propann/dexed/doc/Audio-Chain.png

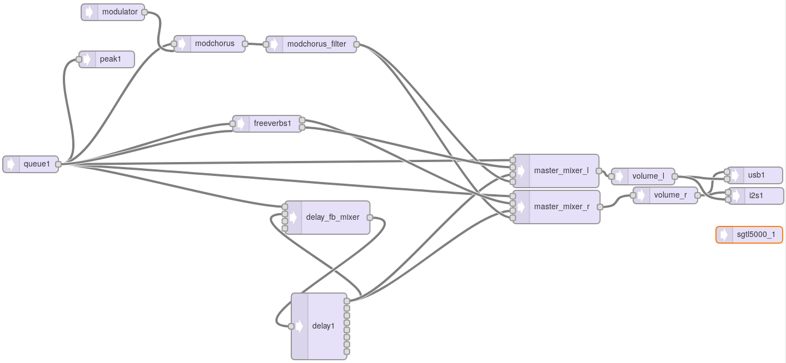
doc/Audio-Chain.png
