propann/dexed/doc/Build_InstructionsV3_Capacitive_Touch/MD_Capacitive_Touch_pcb_overview.png

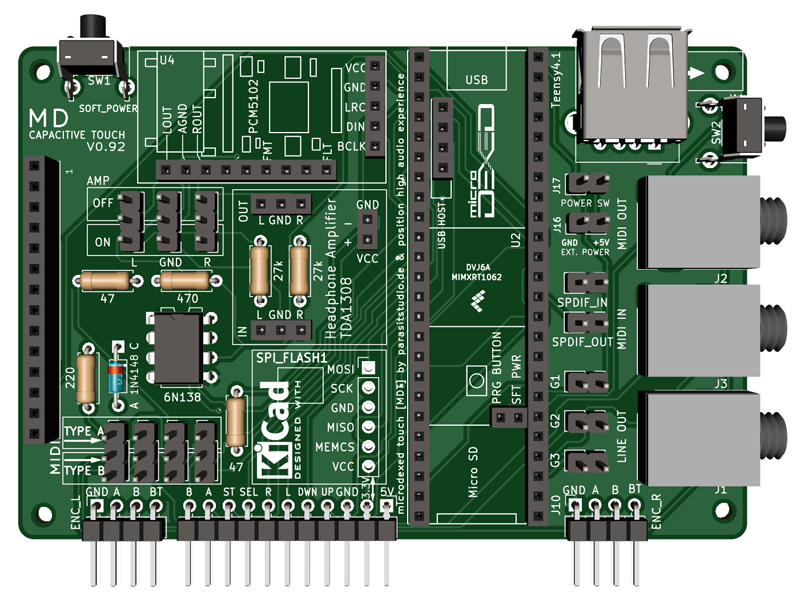
doc/Build_InstructionsV3_Capacitive_Touch/MD_Capacitive_Touch_pcb_overview.png
