propann/dexed/doc/Display-Conversion/back.jpg

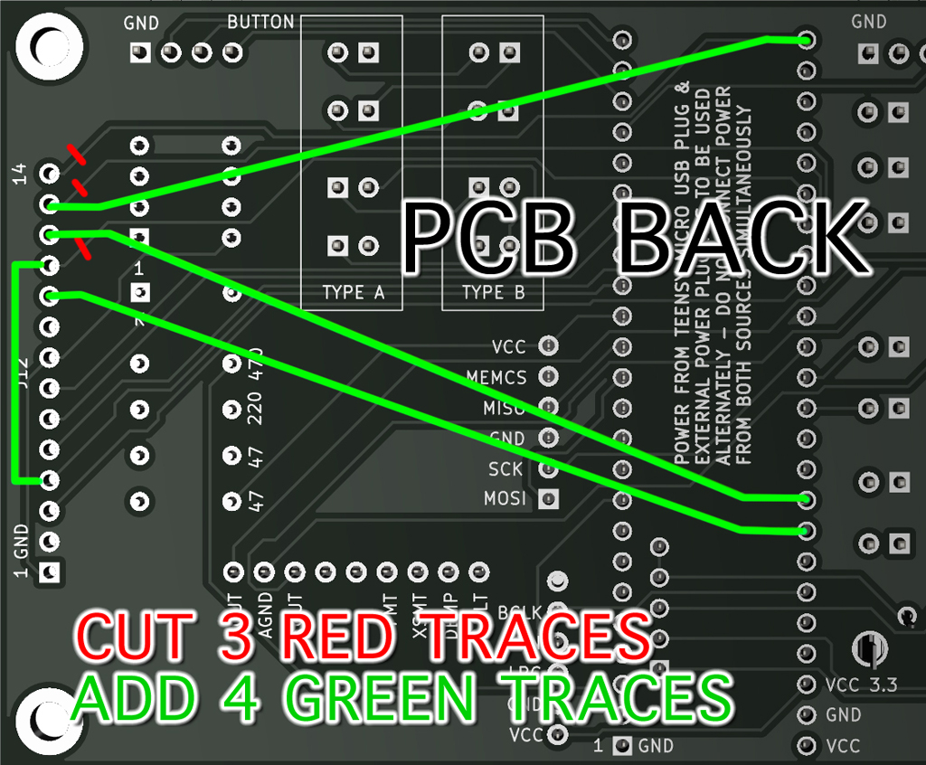
doc/Display-Conversion/back.jpg
