propann/dexed/doc/Display-Conversion/front.jpg

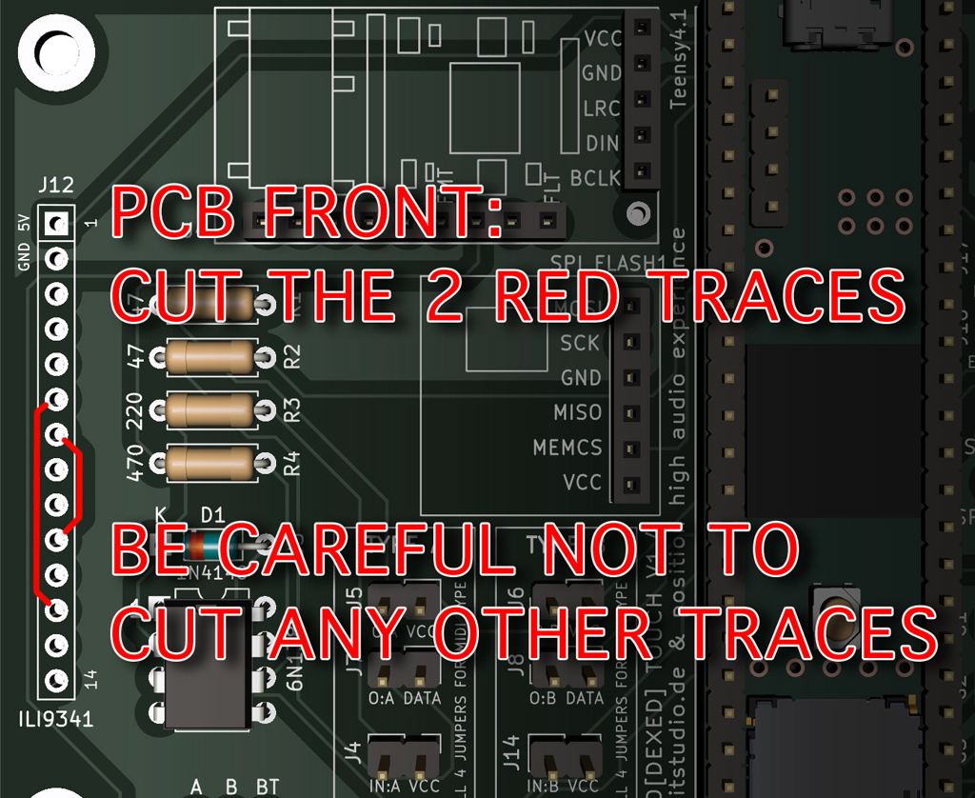
doc/Display-Conversion/front.jpg
