propann/dexed/doc/display-wire.png

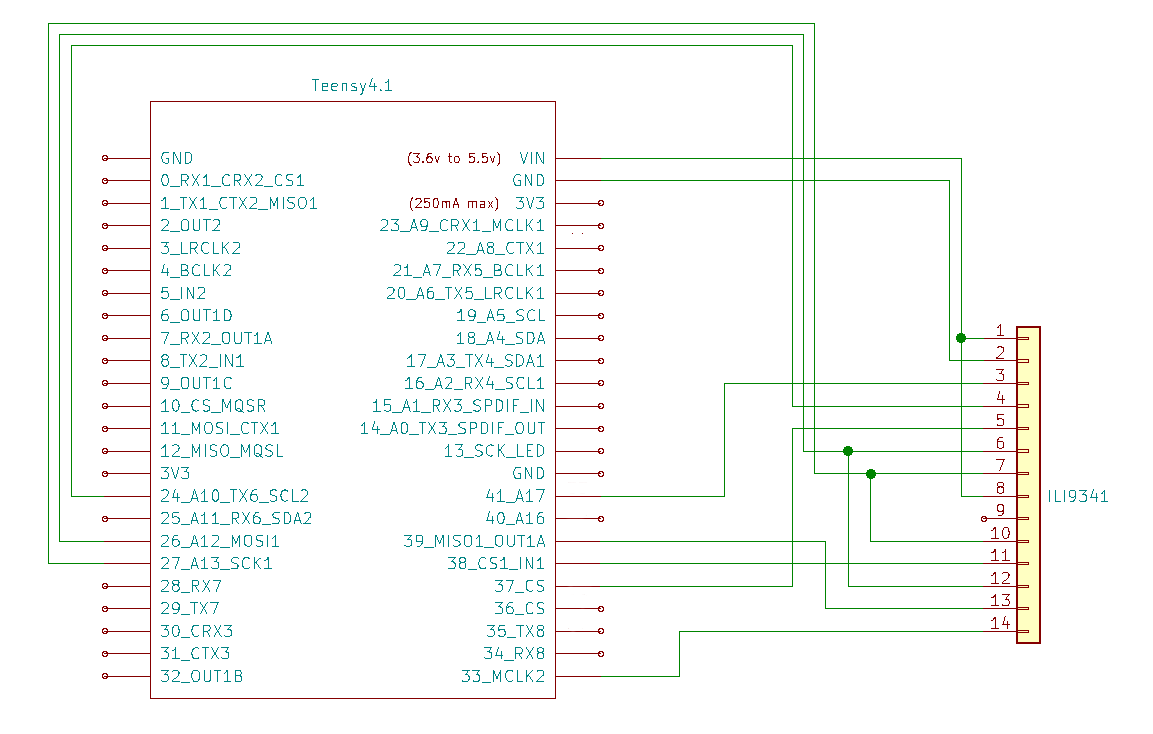
doc/display-wire.png
