propann/dexed/doc/Gamepad/gamepad.png

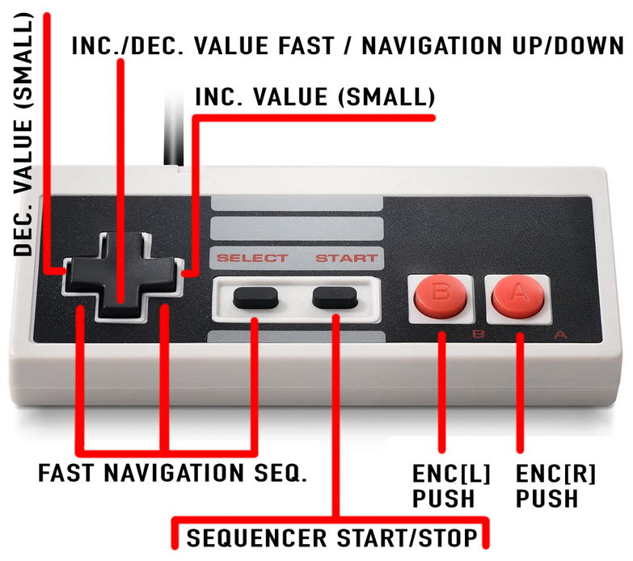
doc/Gamepad/gamepad.png
