propann/dexed/doc/gen1-gen2.jpg

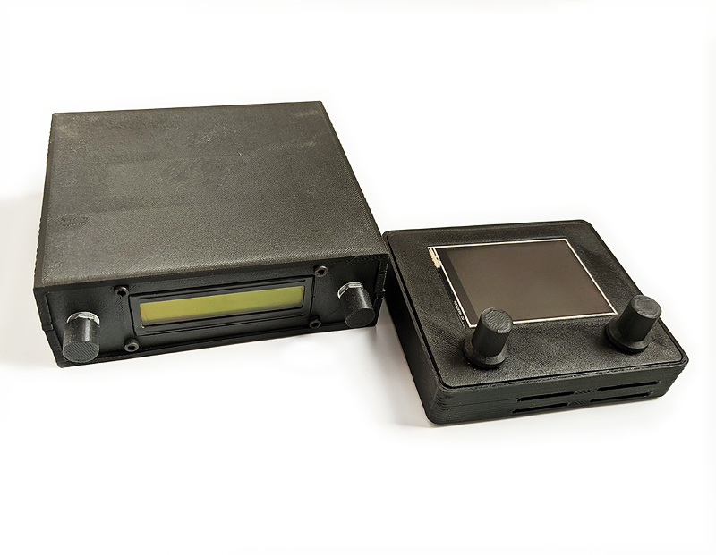
doc/gen1-gen2.jpg
