propann/dexed/doc/MicroDexed-Audio-FlowChart.png

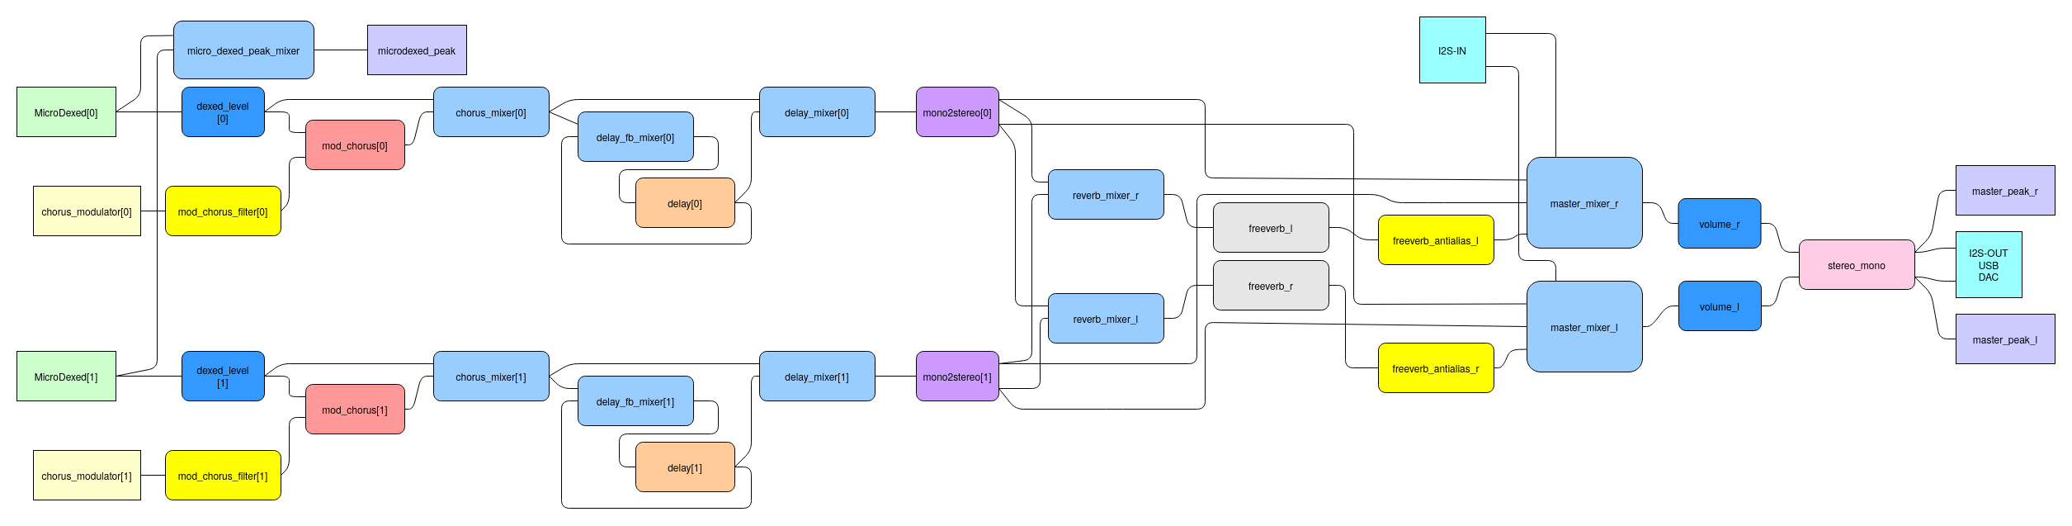
doc/MicroDexed-Audio-FlowChart.png
