propann/dexed/doc/pin_layout_t41.png

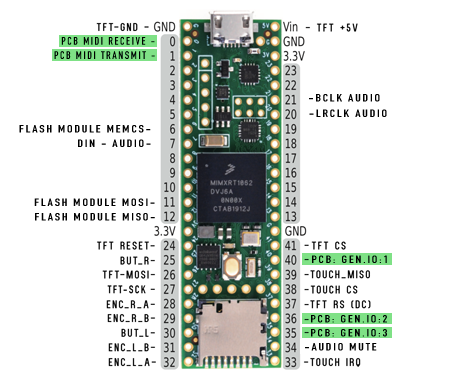
doc/pin_layout_t41.png
