propann/dexed/doc/proto-a-b1.jpg

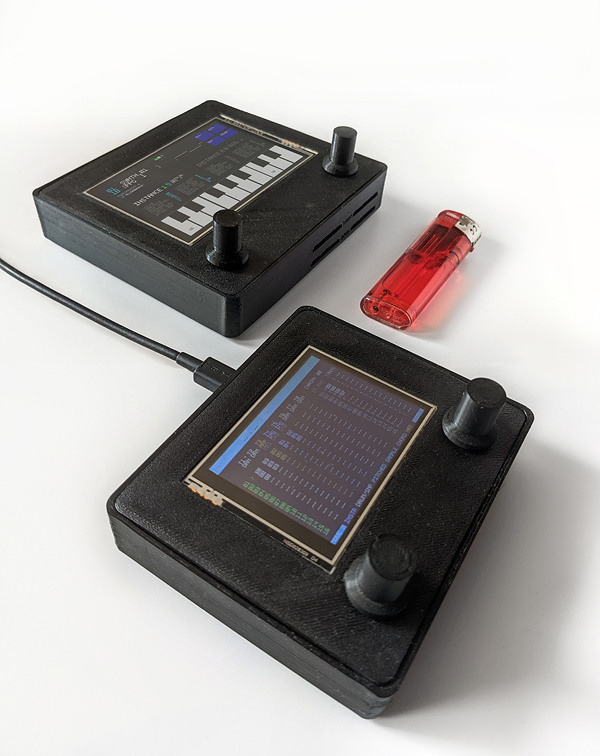
doc/proto-a-b1.jpg
