propann/dexed/doc/proto-b1.jpg

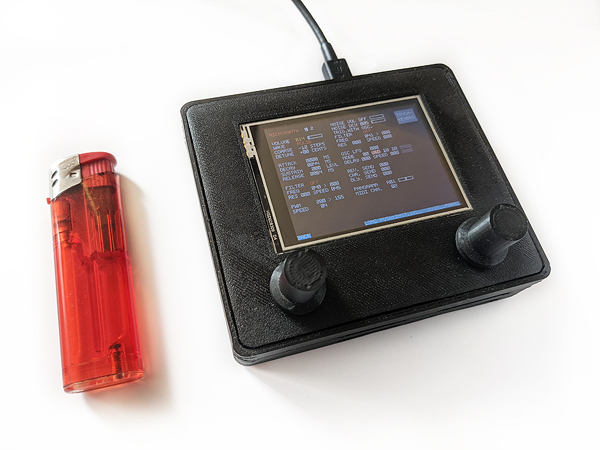
doc/proto-b1.jpg
