propann/dexed/doc/Build_InstructionsV2/assembly_final3.jpg

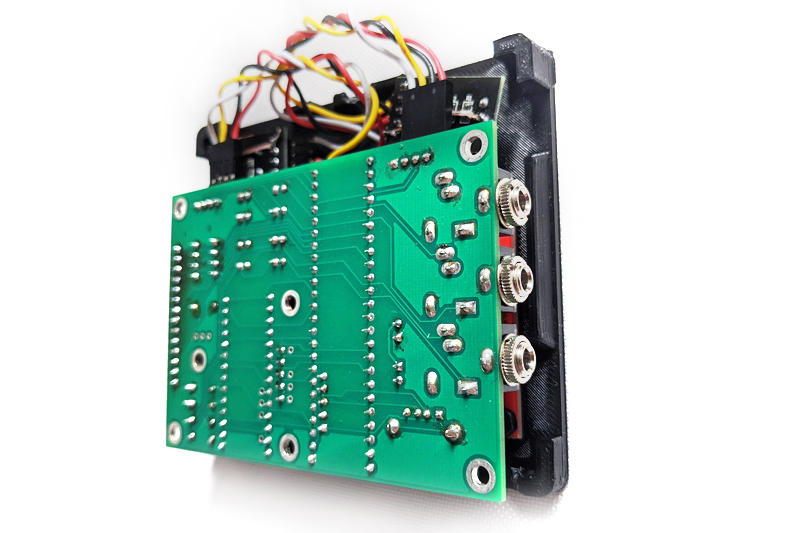
doc/Build_InstructionsV2/assembly_final3.jpg
