propann/dexed/doc/Build_InstructionsV2/assembly_final6.jpg

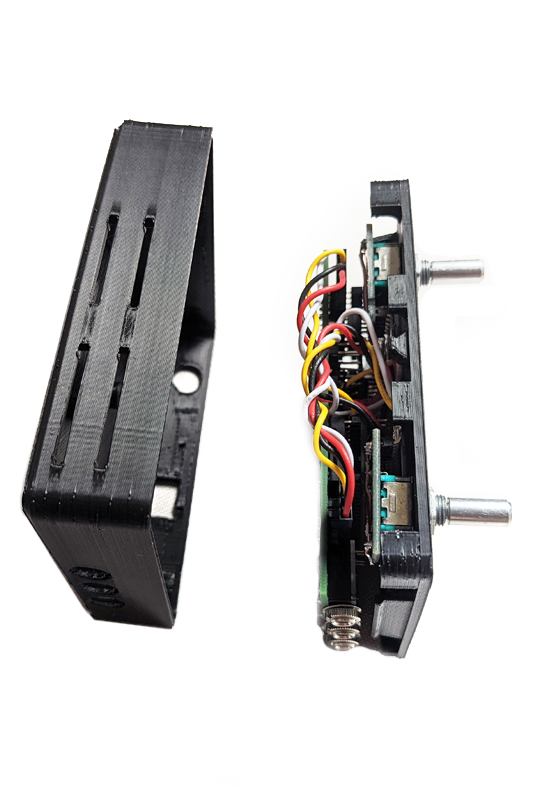
doc/Build_InstructionsV2/assembly_final6.jpg
