propann/dexed/doc/Build_InstructionsV2/back-c.png

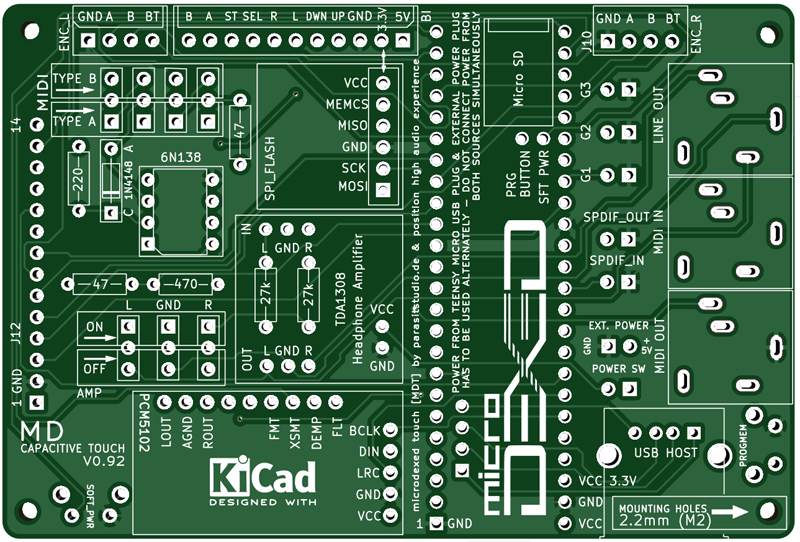
doc/Build_InstructionsV2/back-c.png
