propann/dexed/doc/Build_InstructionsV2/board-assembled3.png

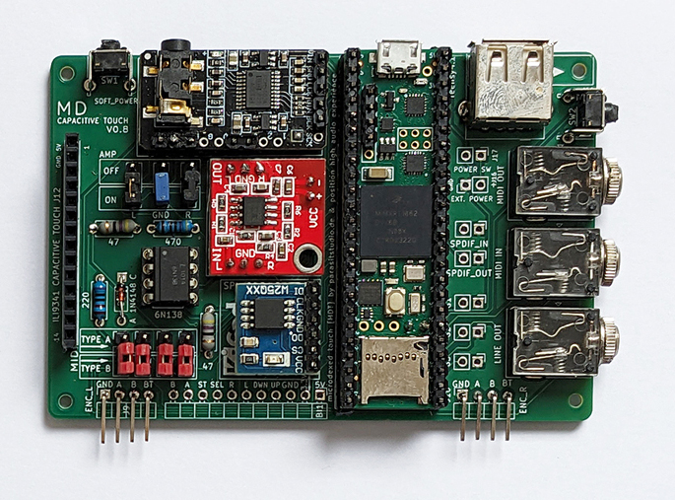
doc/Build_InstructionsV2/board-assembled3.png
