propann/dexed/doc/Build_InstructionsV2/board-with-flash2.png

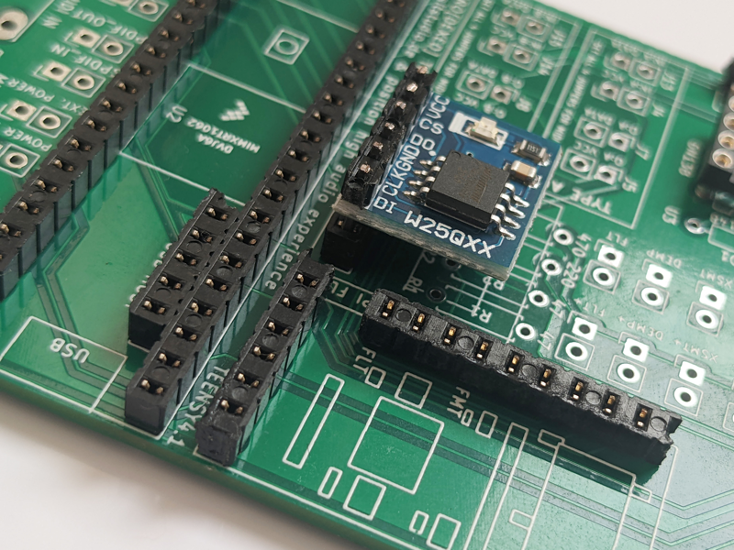
doc/Build_InstructionsV2/board-with-flash2.png
