propann/dexed/doc/Build_InstructionsV2/board-with-flash-c.png

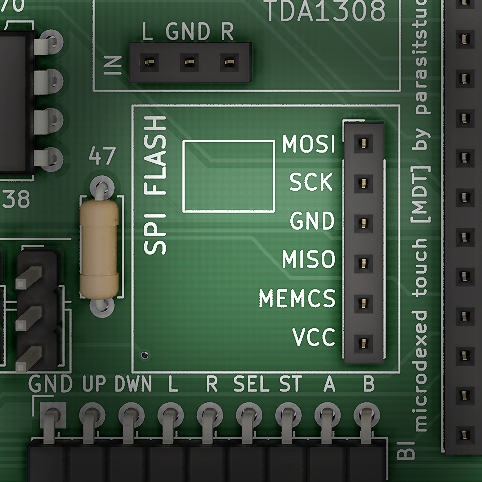
doc/Build_InstructionsV2/board-with-flash-c.png
