propann/dexed/doc/Build_InstructionsV2/board-with-flash.png

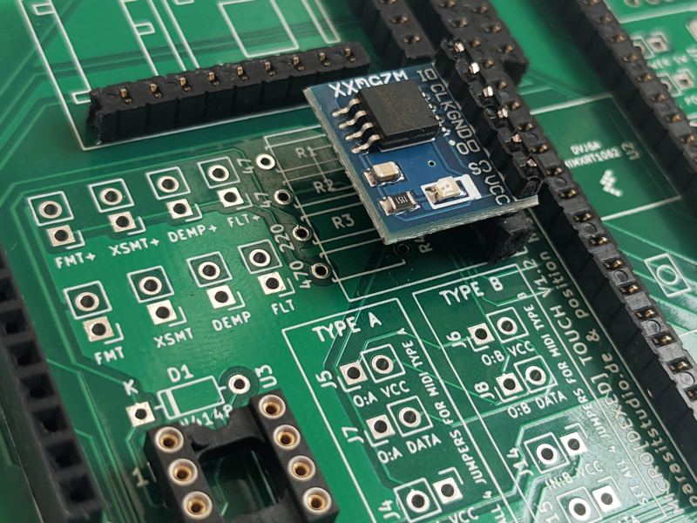
doc/Build_InstructionsV2/board-with-flash.png
