propann/dexed/doc/Build_InstructionsV2/board-with-sockets1.png

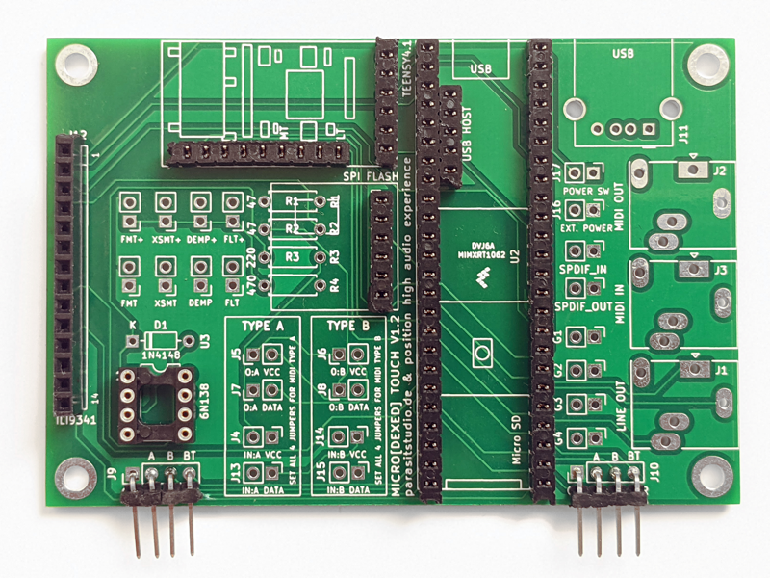
doc/Build_InstructionsV2/board-with-sockets1.png
