propann/dexed/doc/Build_InstructionsV2/board-with-sockets2.png

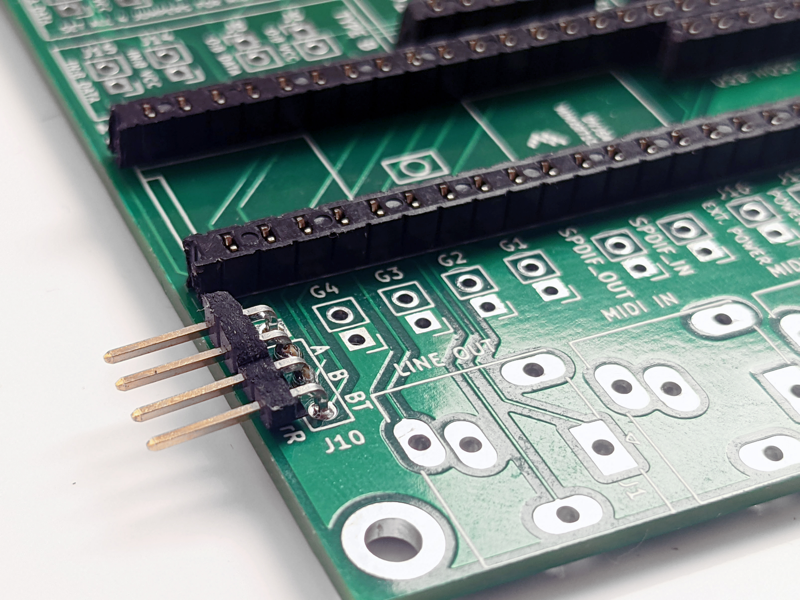
doc/Build_InstructionsV2/board-with-sockets2.png
