propann/dexed/doc/Build_InstructionsV2/bottomcase.png

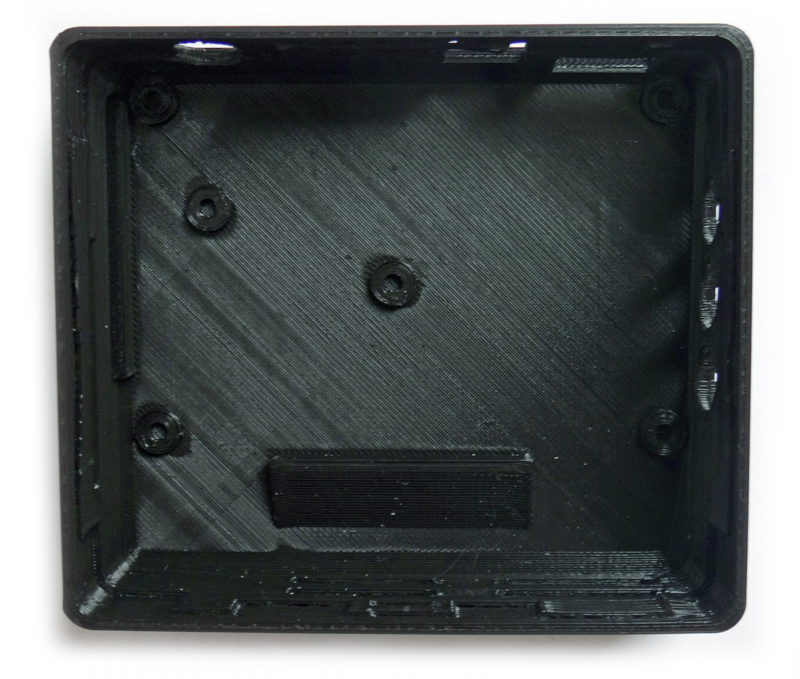
doc/Build_InstructionsV2/bottomcase.png
