propann/dexed/doc/Build_InstructionsV2/case-sdmod-lid-cover.png

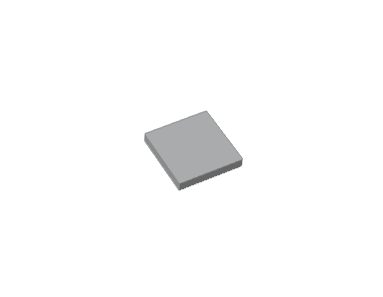
doc/Build_InstructionsV2/case-sdmod-lid-cover.png
