propann/dexed/doc/Build_InstructionsV2/case-sdmod-lid.png

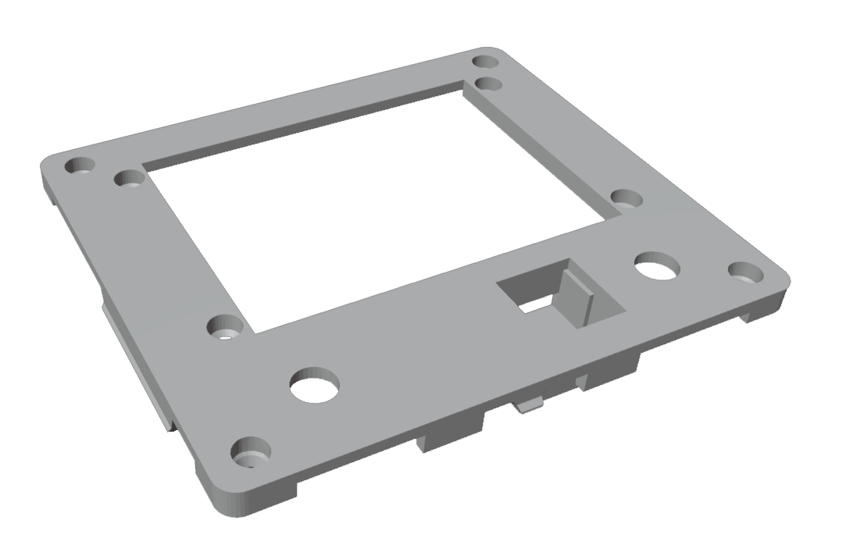
doc/Build_InstructionsV2/case-sdmod-lid.png
