propann/dexed/doc/Build_InstructionsV2/case.png

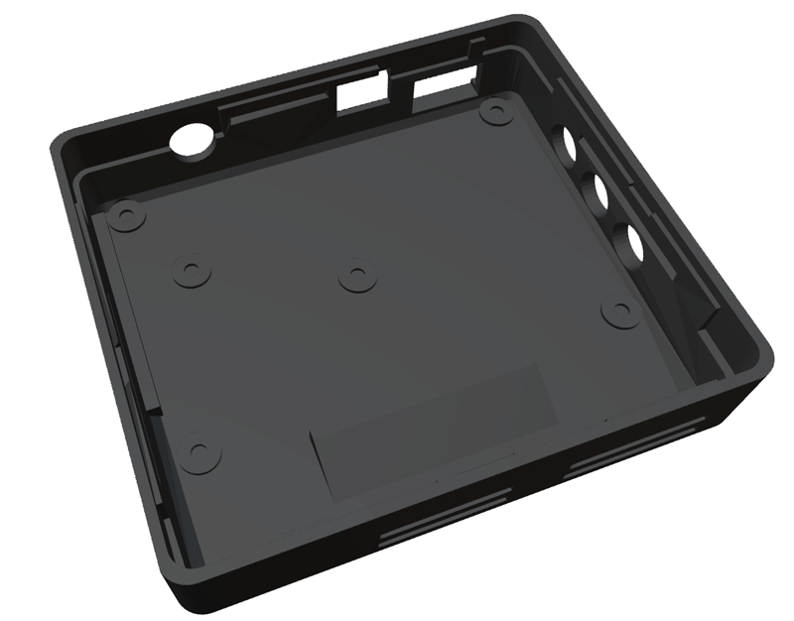
doc/Build_InstructionsV2/case.png
