propann/dexed/doc/Build_InstructionsV2/case_0.jpg

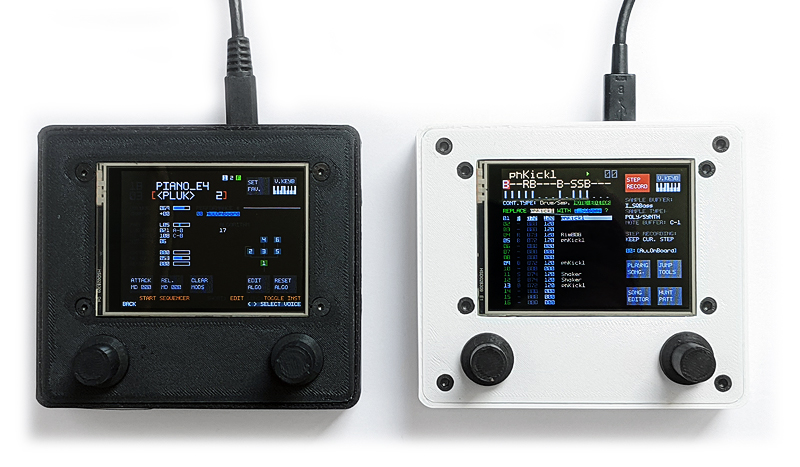
doc/Build_InstructionsV2/case_0.jpg
