propann/dexed/doc/Build_InstructionsV2/case_1.jpg

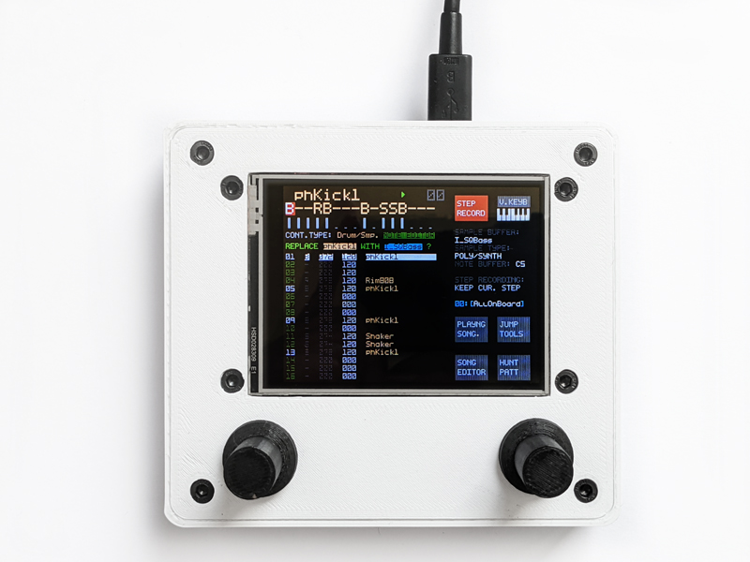
doc/Build_InstructionsV2/case_1.jpg
