propann/dexed/doc/Build_InstructionsV2/case_2.jpg

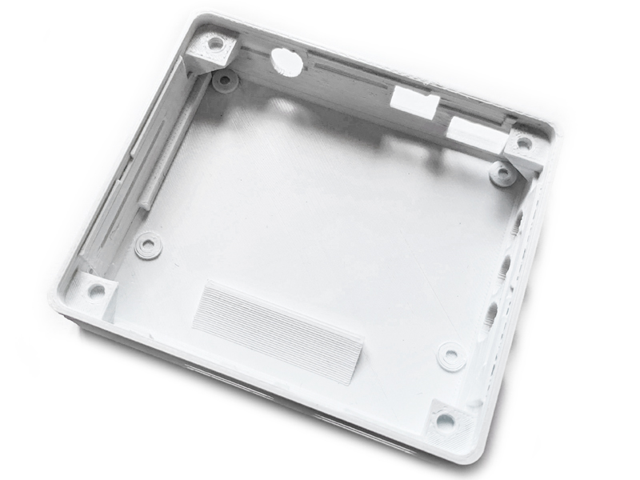
doc/Build_InstructionsV2/case_2.jpg
