propann/dexed/doc/Build_InstructionsV2/case_3.jpg

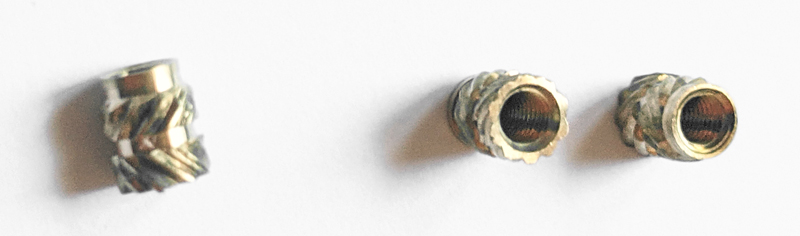
doc/Build_InstructionsV2/case_3.jpg
