propann/dexed/doc/Build_InstructionsV2/case_3b.jpg

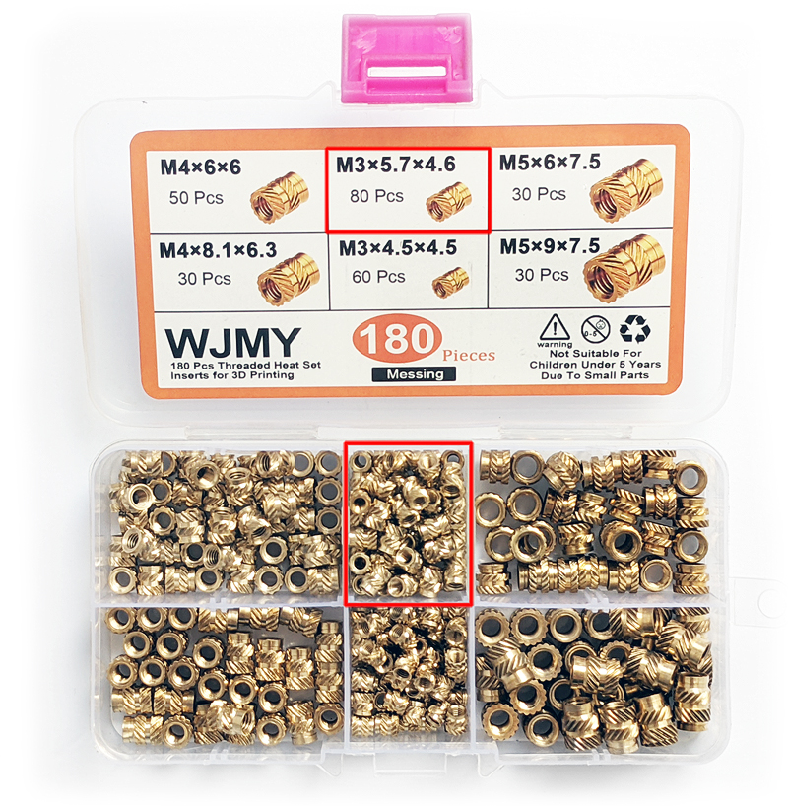
doc/Build_InstructionsV2/case_3b.jpg
