propann/dexed/doc/Build_InstructionsV2/case_4.jpg

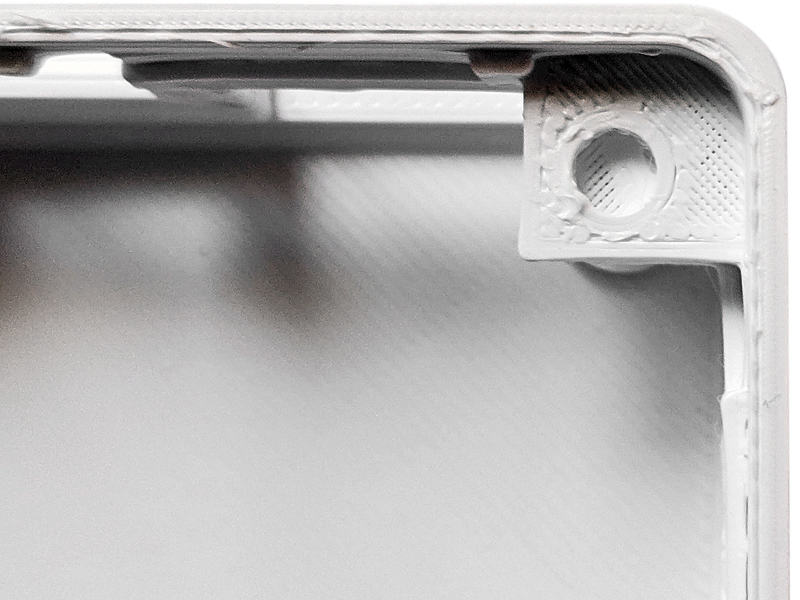
doc/Build_InstructionsV2/case_4.jpg
