propann/dexed/doc/Build_InstructionsV2/case_5.jpg

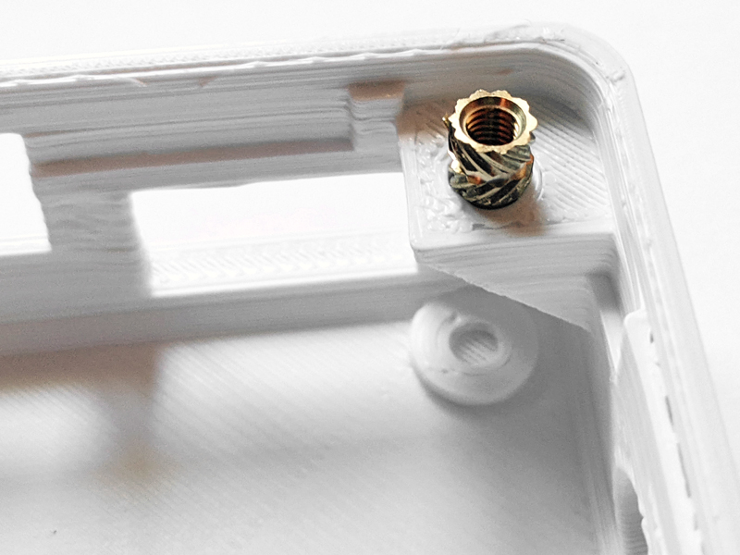
doc/Build_InstructionsV2/case_5.jpg
