propann/dexed/doc/Build_InstructionsV2/case_6.jpg

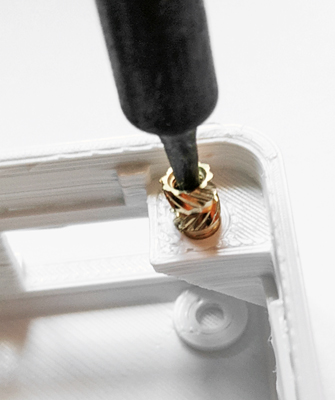
doc/Build_InstructionsV2/case_6.jpg
