propann/dexed/doc/Build_InstructionsV2/case_7.jpg

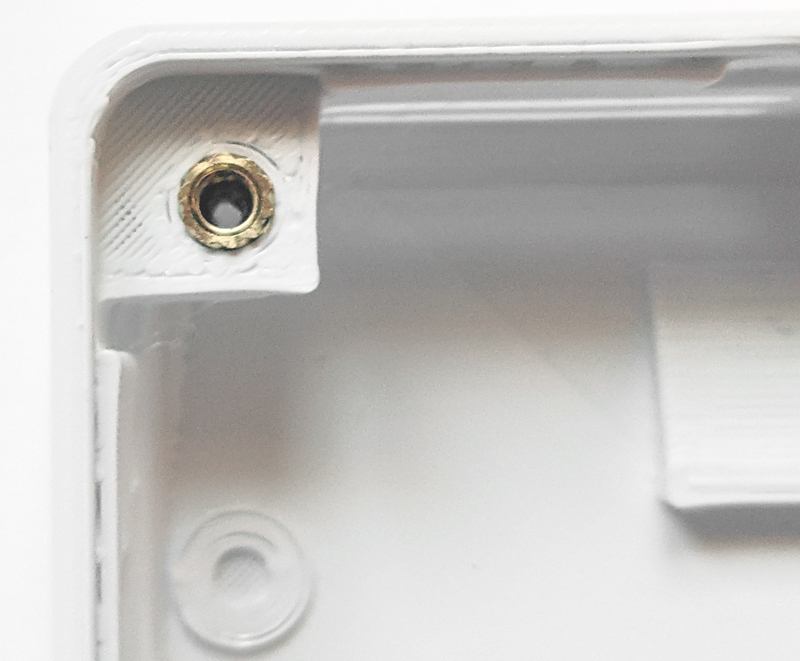
doc/Build_InstructionsV2/case_7.jpg
