propann/dexed/doc/Build_InstructionsV2/case_8.jpg

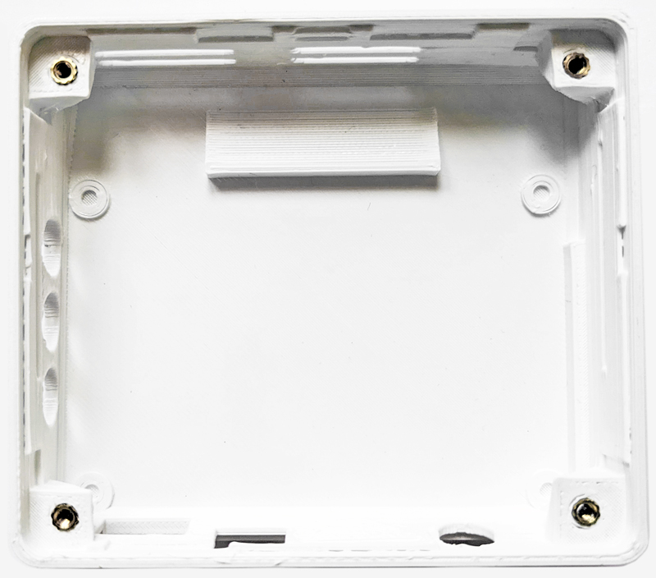
doc/Build_InstructionsV2/case_8.jpg
