propann/dexed/doc/Build_InstructionsV2/case_9.jpg

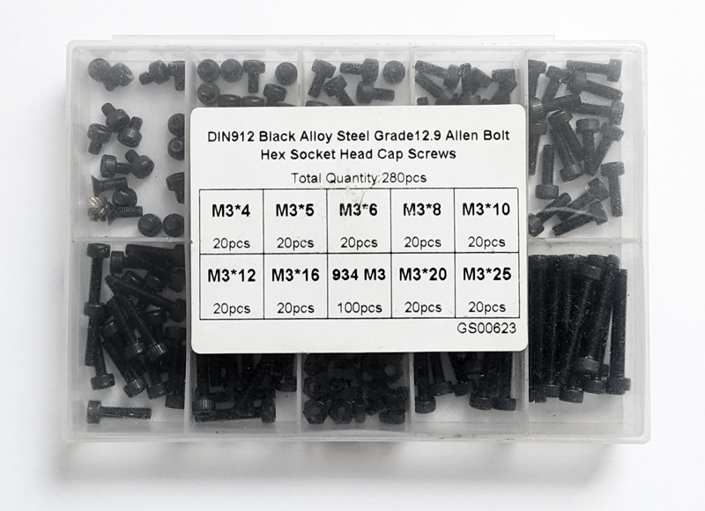
doc/Build_InstructionsV2/case_9.jpg
