propann/dexed/doc/Build_InstructionsV2/case_10.jpg

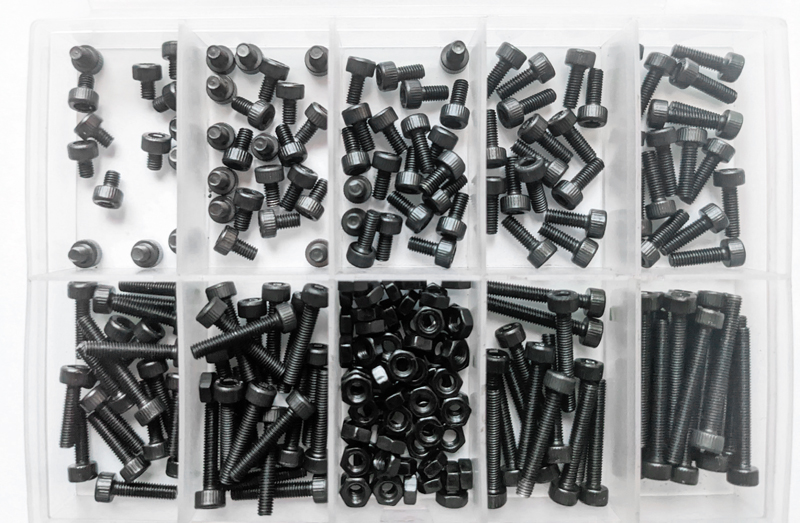
doc/Build_InstructionsV2/case_10.jpg
