propann/dexed/doc/Build_InstructionsV2/case_11.jpg

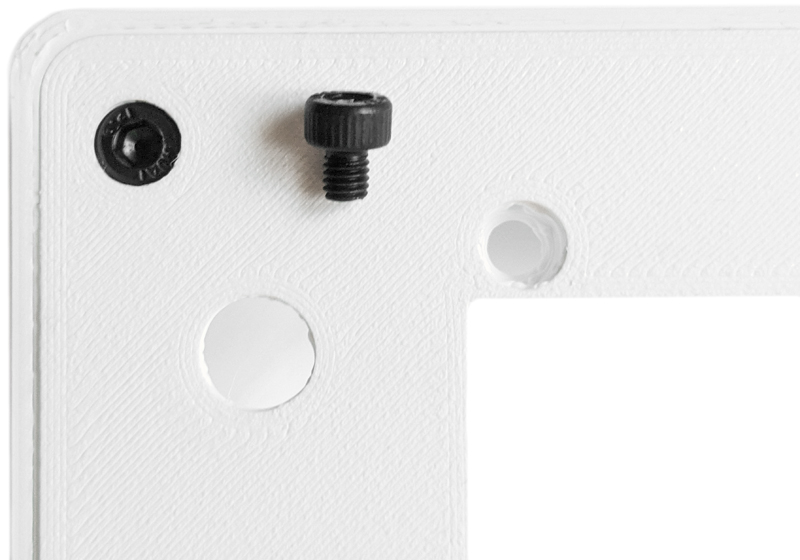
doc/Build_InstructionsV2/case_11.jpg
