propann/dexed/doc/Build_InstructionsV2/case_12.jpg

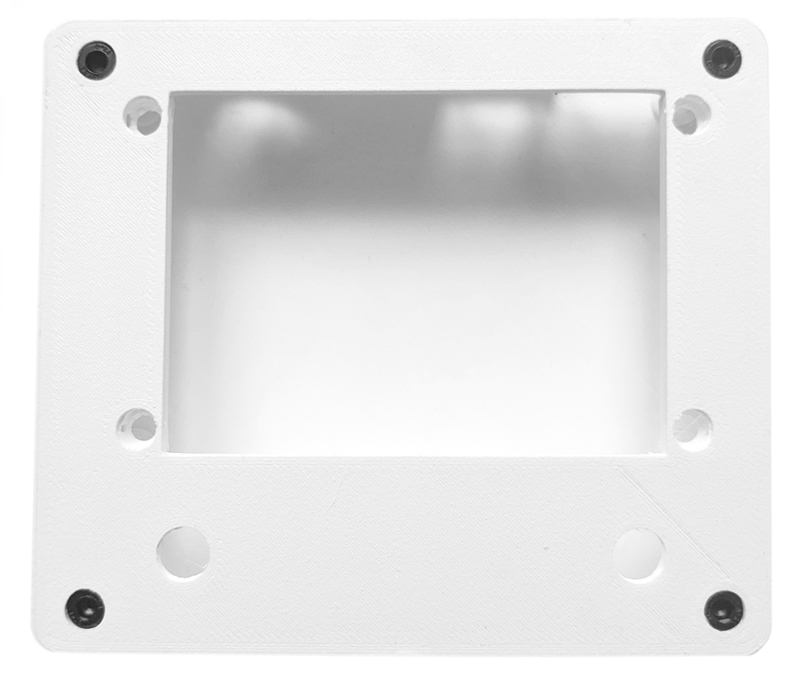
doc/Build_InstructionsV2/case_12.jpg
