propann/dexed/doc/Build_InstructionsV2/case_13.jpg

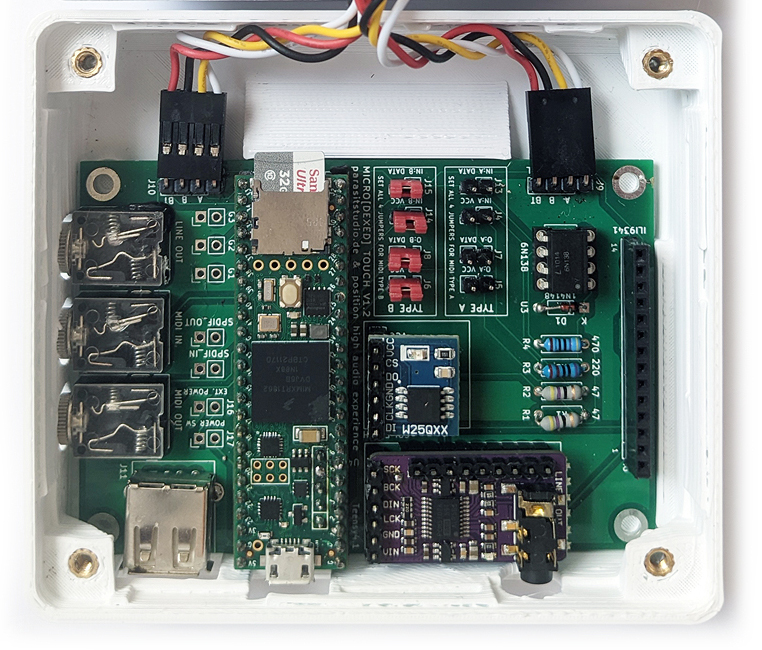
doc/Build_InstructionsV2/case_13.jpg
