propann/dexed/doc/Build_InstructionsV2/case_14.png

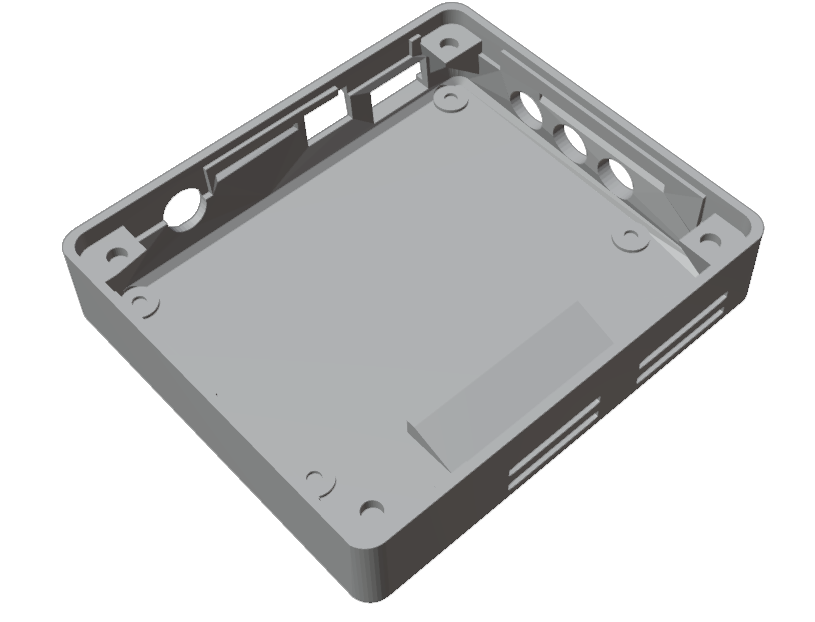
doc/Build_InstructionsV2/case_14.png
