propann/dexed/doc/Build_InstructionsV2/case_15.png

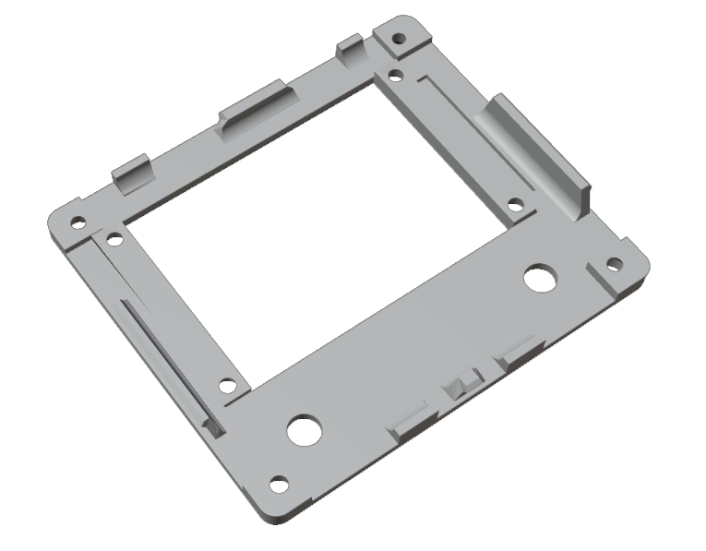
doc/Build_InstructionsV2/case_15.png
