propann/dexed/doc/Build_InstructionsV2/case_16.png

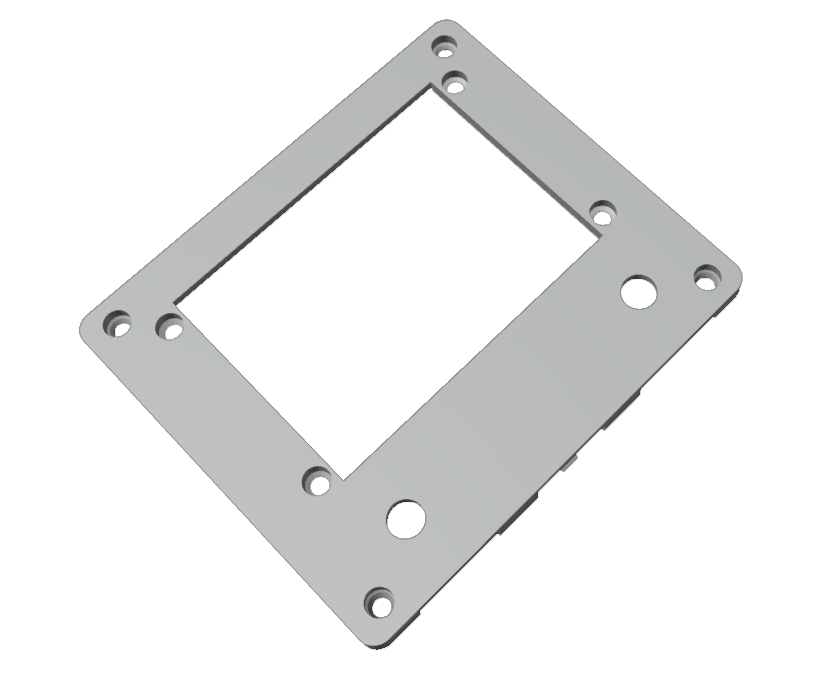
doc/Build_InstructionsV2/case_16.png
