propann/dexed/doc/Build_InstructionsV2/displayconnector2-c.png

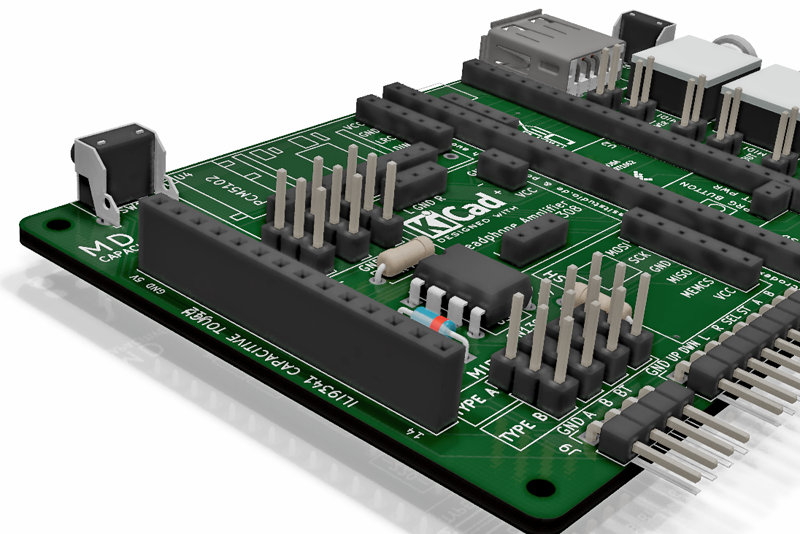
doc/Build_InstructionsV2/displayconnector2-c.png
