propann/dexed/doc/Build_InstructionsV2/displayconnector2.png

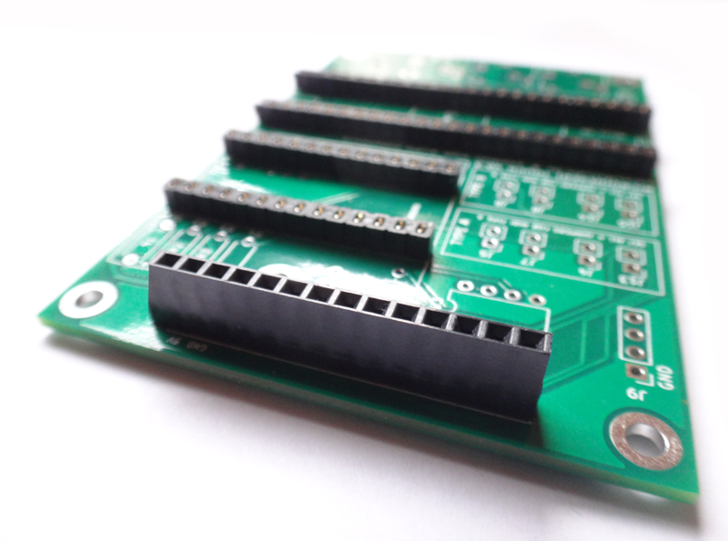
doc/Build_InstructionsV2/displayconnector2.png
