propann/dexed/doc/Build_InstructionsV2/displayconnector.png

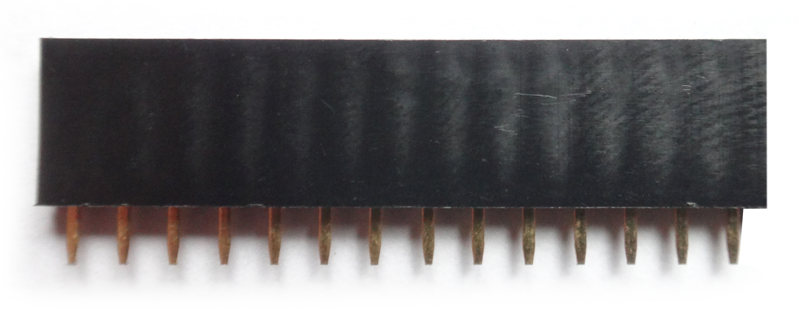
doc/Build_InstructionsV2/displayconnector.png
