propann/dexed/doc/Build_InstructionsV2/encoderconnector.png

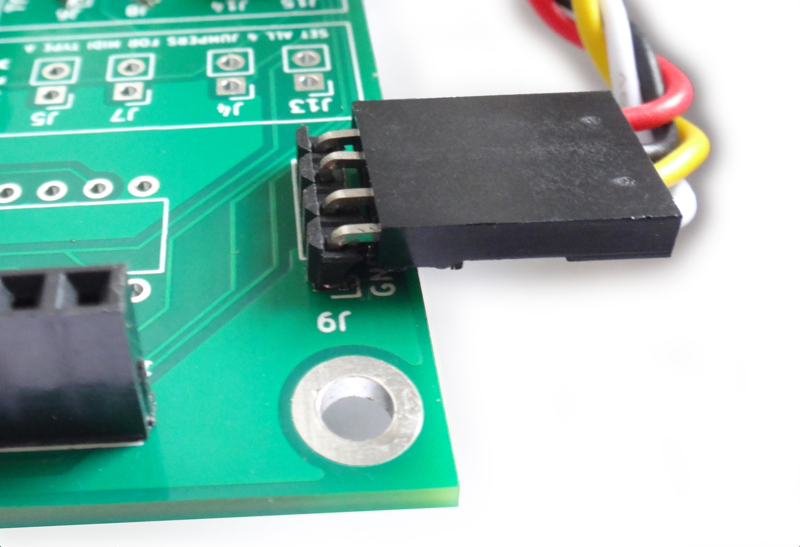
doc/Build_InstructionsV2/encoderconnector.png
