propann/dexed/doc/Build_InstructionsV2/external-flash1.png

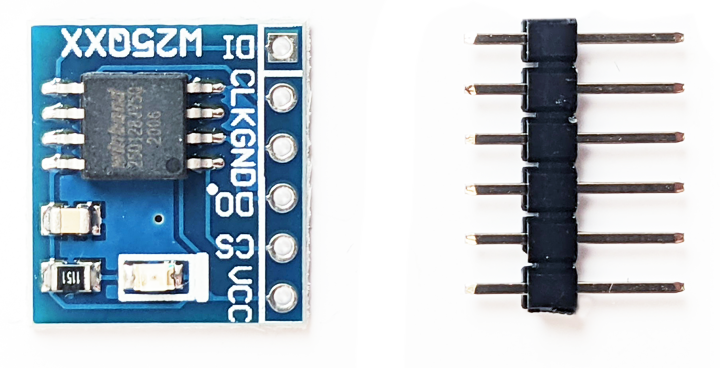
doc/Build_InstructionsV2/external-flash1.png
