propann/dexed/doc/Build_InstructionsV2/external-flash2.png

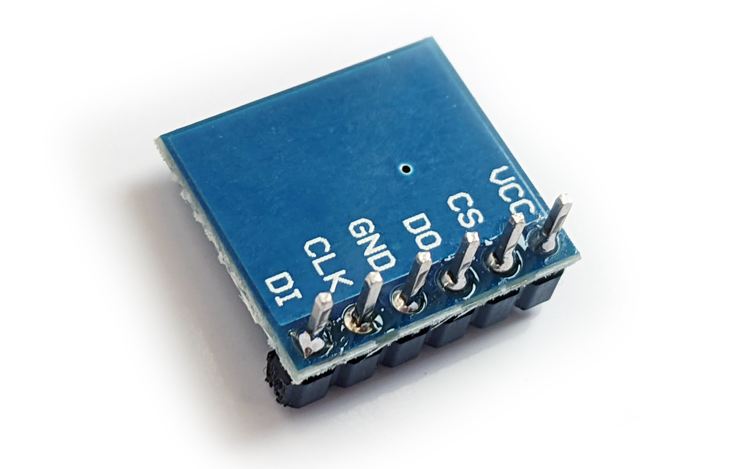
doc/Build_InstructionsV2/external-flash2.png
