propann/dexed/doc/Build_InstructionsV2/external-flash3.png

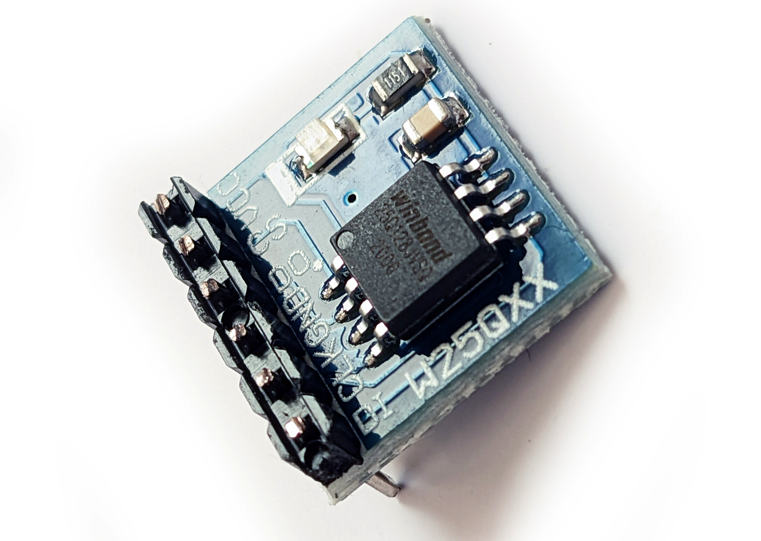
doc/Build_InstructionsV2/external-flash3.png
