propann/dexed/doc/Build_InstructionsV2/external-flash4.png

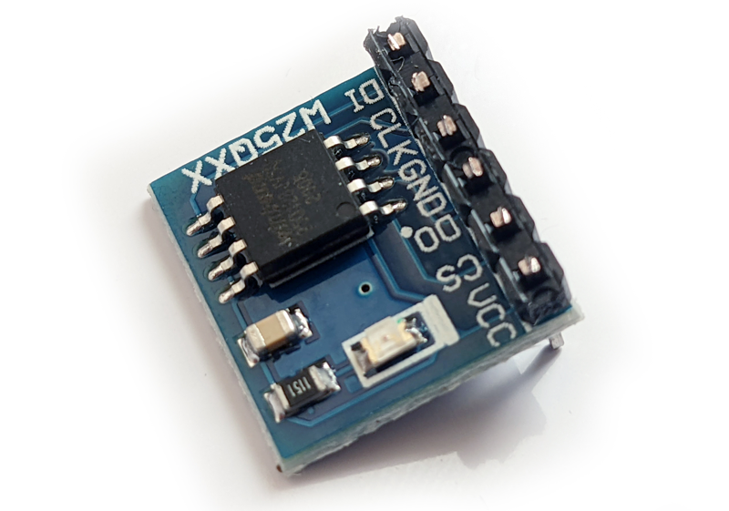
doc/Build_InstructionsV2/external-flash4.png
