propann/dexed/doc/Build_InstructionsV2/final1.png

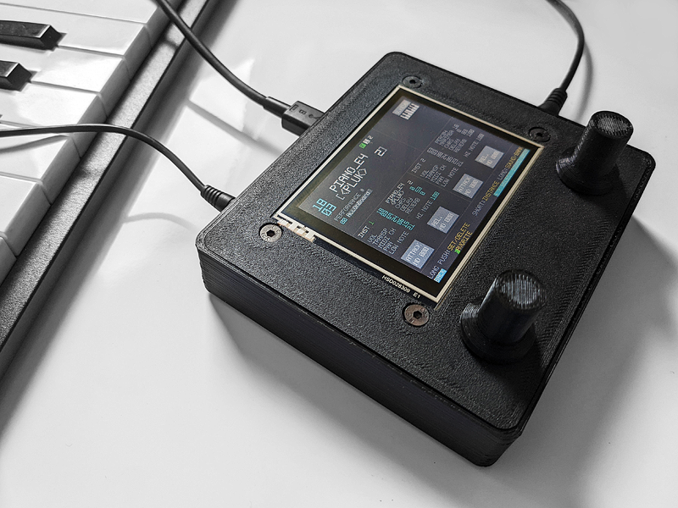
doc/Build_InstructionsV2/final1.png
