propann/dexed/doc/Build_InstructionsV2/final2.png

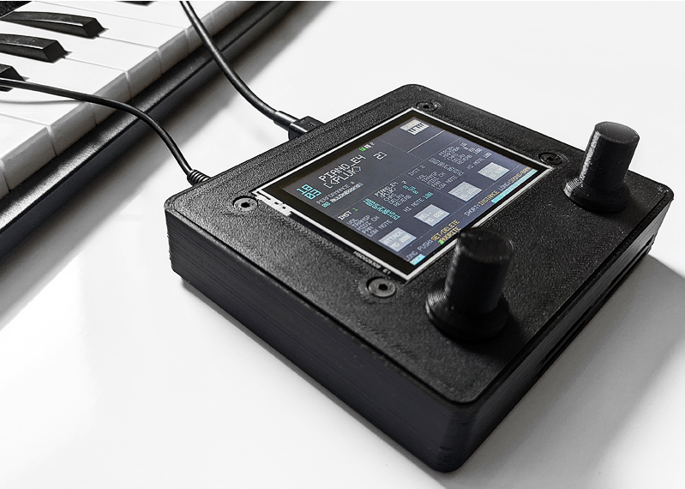
doc/Build_InstructionsV2/final2.png
