propann/dexed/doc/Build_InstructionsV2/finalwithencoders.png

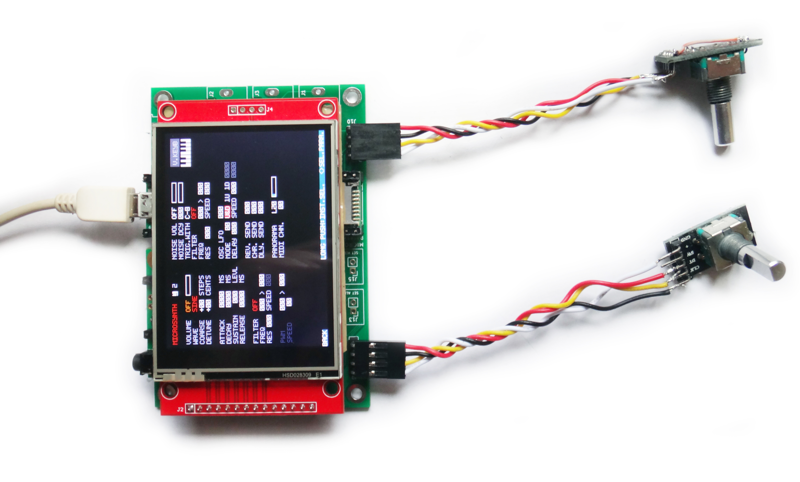
doc/Build_InstructionsV2/finalwithencoders.png
