propann/dexed/doc/Build_InstructionsV2/front-c.png

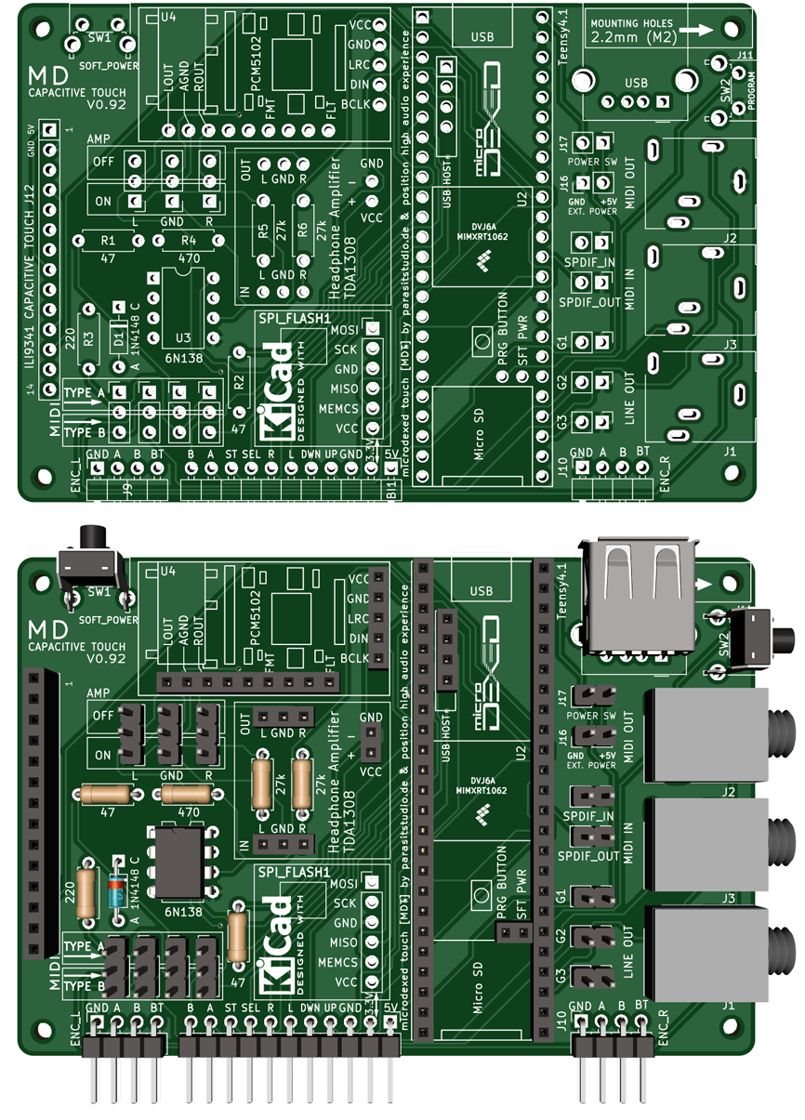
doc/Build_InstructionsV2/front-c.png
