propann/dexed/doc/Build_InstructionsV2/heightview.png

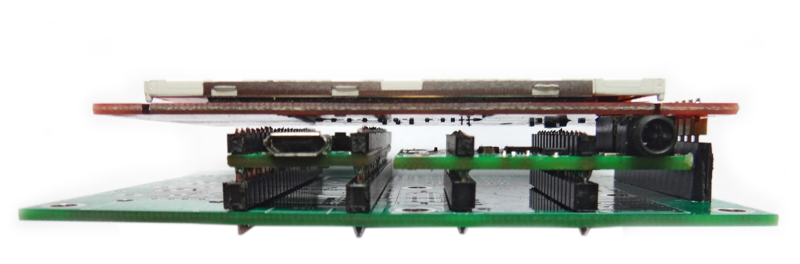
doc/Build_InstructionsV2/heightview.png
