propann/dexed/doc/Build_InstructionsV2/lid.png

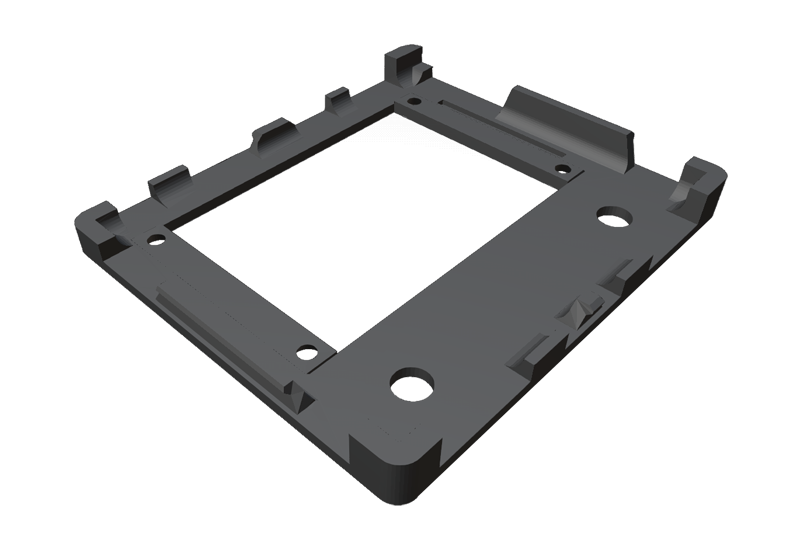
doc/Build_InstructionsV2/lid.png
