propann/dexed/doc/Build_InstructionsV2/pcm1.png

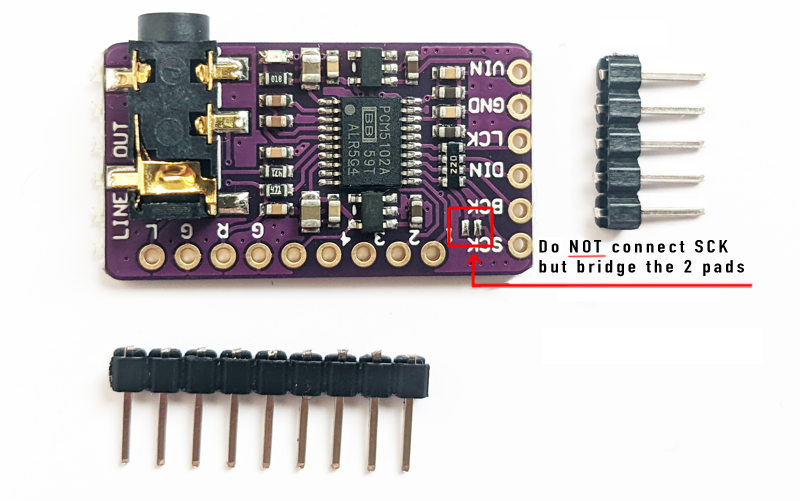
doc/Build_InstructionsV2/pcm1.png
