propann/dexed/doc/Build_InstructionsV2/pcm2.png

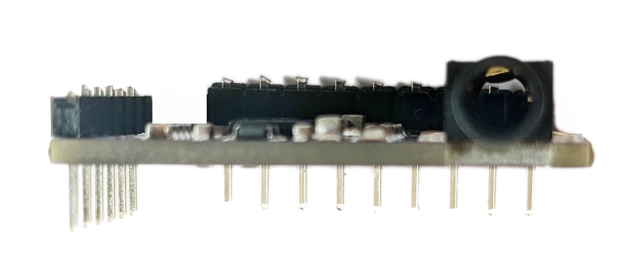
doc/Build_InstructionsV2/pcm2.png
