propann/dexed/doc/Build_InstructionsV2/pcm3.png

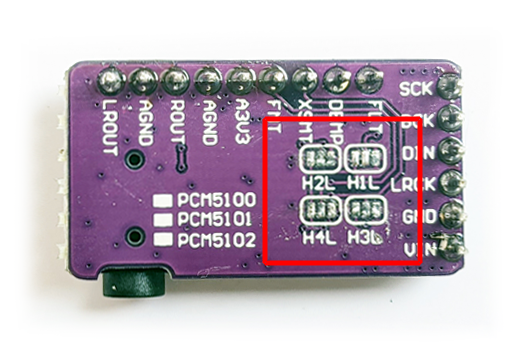
doc/Build_InstructionsV2/pcm3.png
