propann/dexed/doc/Build_InstructionsV2/pcm4.png

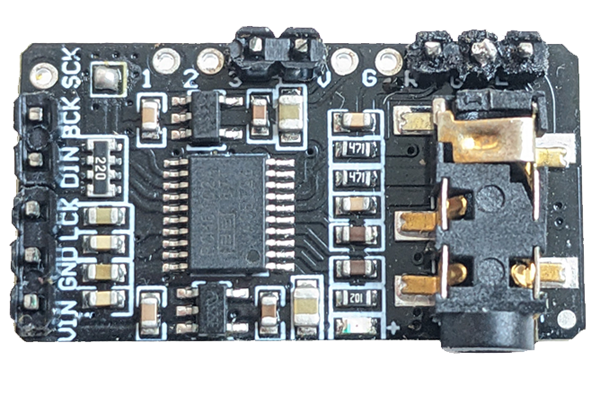
doc/Build_InstructionsV2/pcm4.png
