propann/dexed/doc/Build_InstructionsV2/pinsandsocket.png

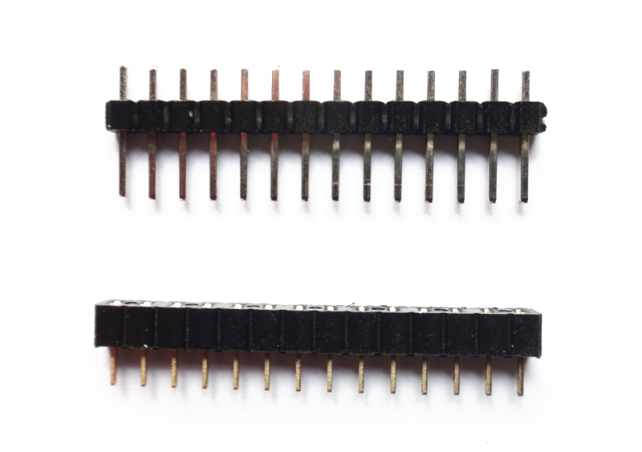
doc/Build_InstructionsV2/pinsandsocket.png
