propann/dexed/doc/Build_InstructionsV2/recorder_1.png

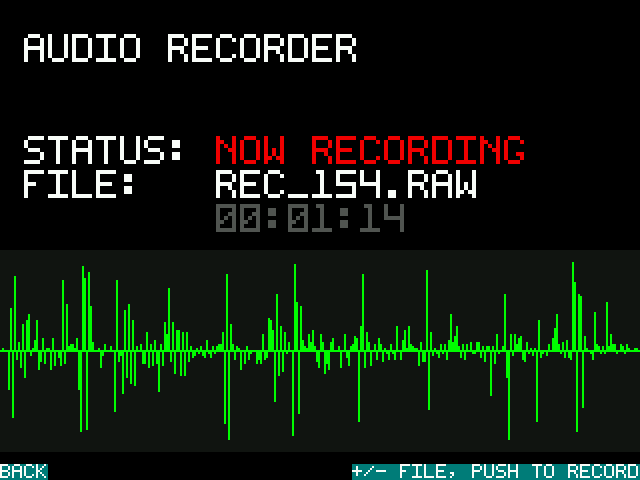
doc/Build_InstructionsV2/recorder_1.png
