propann/dexed/doc/Build_InstructionsV2/recorder_2.png

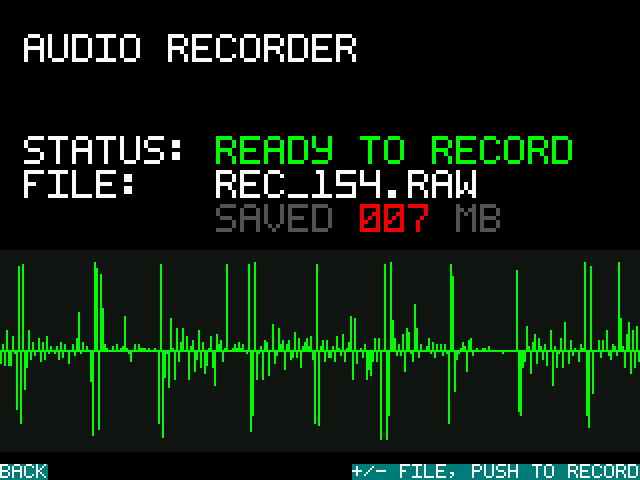
doc/Build_InstructionsV2/recorder_2.png
