propann/dexed/doc/Build_InstructionsV2/recorder_import-raw.png

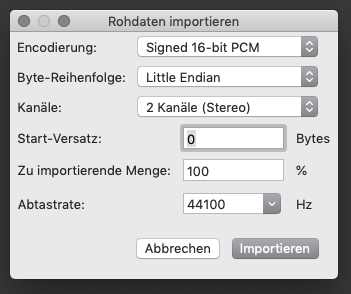
doc/Build_InstructionsV2/recorder_import-raw.png
