propann/dexed/doc/Build_InstructionsV2/resistors-c.png

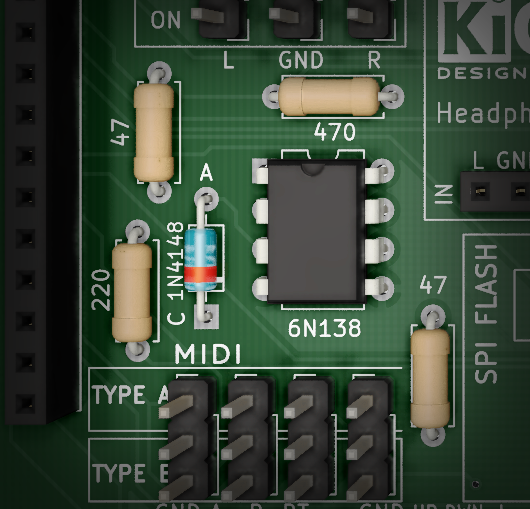
doc/Build_InstructionsV2/resistors-c.png
