propann/dexed/doc/Build_InstructionsV2/sdcard.jpg

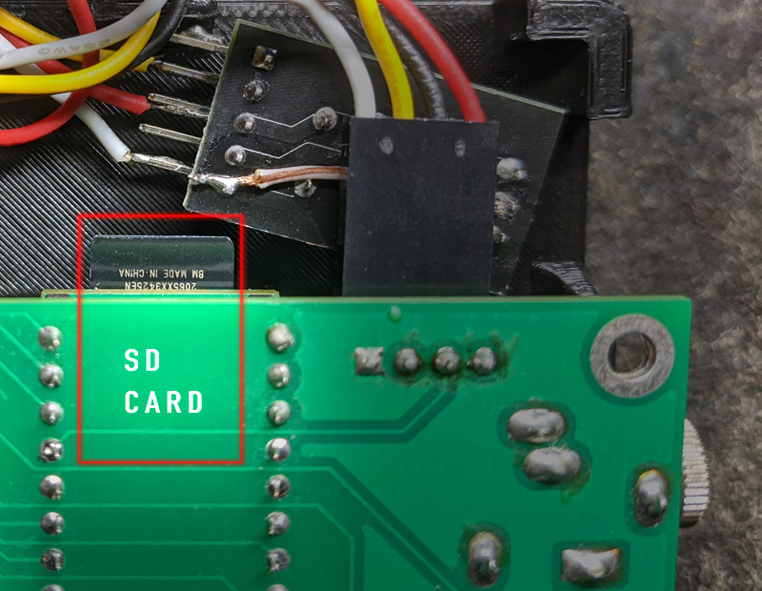
doc/Build_InstructionsV2/sdcard.jpg
