propann/dexed/doc/Build_InstructionsV2/teensywithheader.png

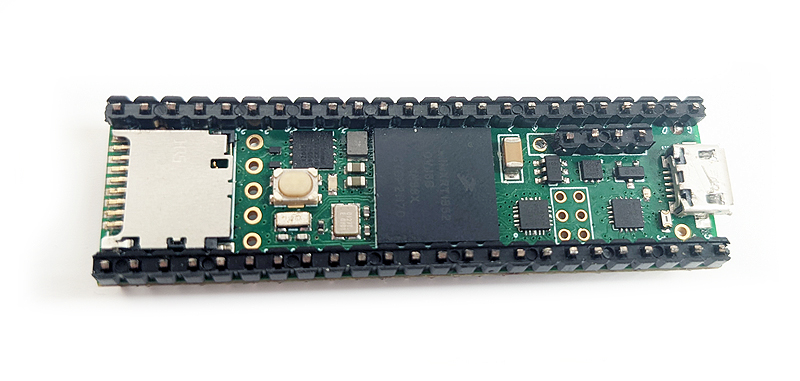
doc/Build_InstructionsV2/teensywithheader.png
