propann/dexed/doc/Build_InstructionsV2/usbsocket-c.png

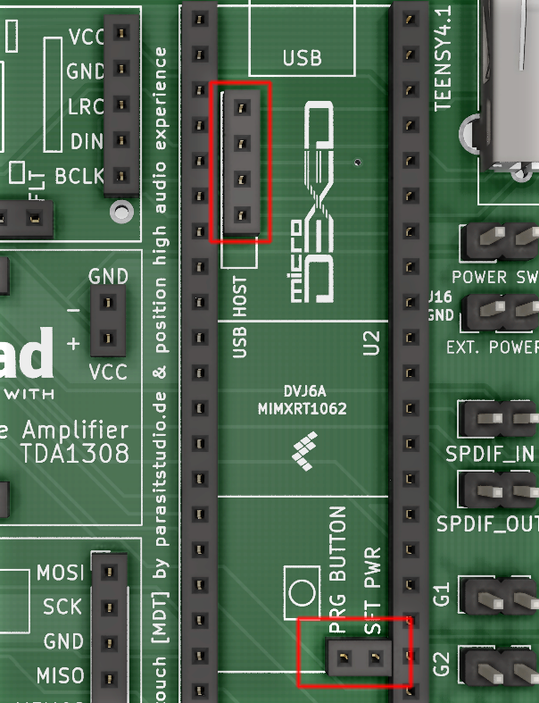
doc/Build_InstructionsV2/usbsocket-c.png
