propann/dexed/doc/Build_InstructionsV2/usbsocket.png

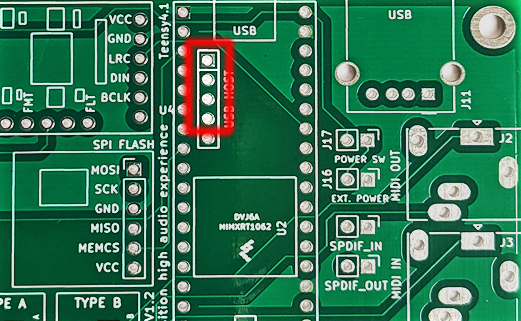
doc/Build_InstructionsV2/usbsocket.png
