propann/dexed/doc/Build_InstructionsV3_Capacitive_Touch/all_low_sockets.png

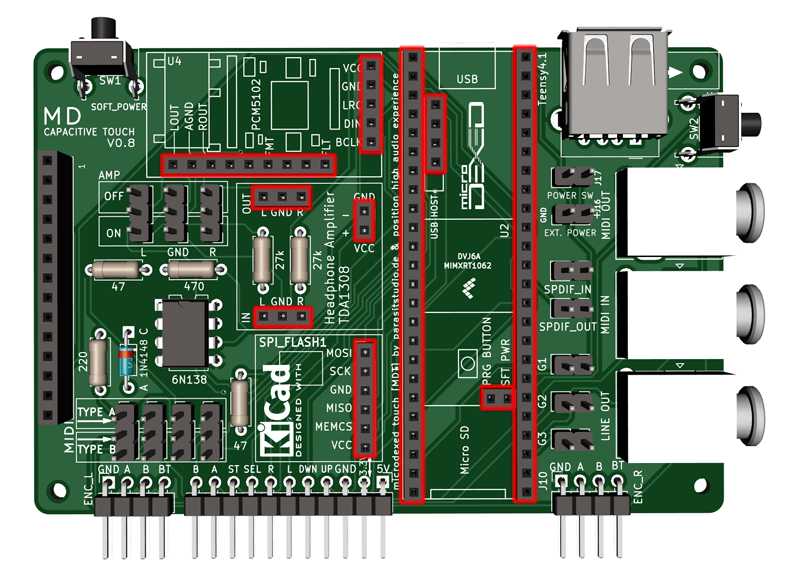
doc/Build_InstructionsV3_Capacitive_Touch/all_low_sockets.png
