propann/dexed/doc/Build_InstructionsV3_Capacitive_Touch/BOTTOM-capacitive_touch.png

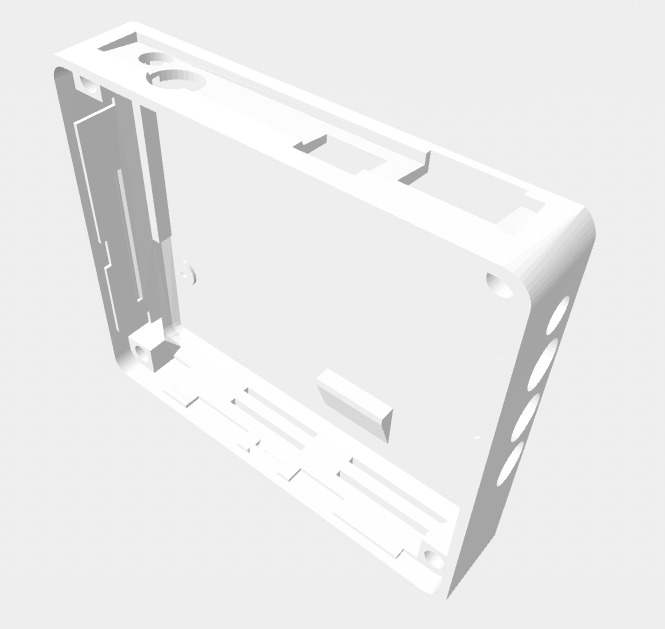
doc/Build_InstructionsV3_Capacitive_Touch/BOTTOM-capacitive_touch.png
