propann/dexed/doc/Build_InstructionsV3_Capacitive_Touch/display_connector2.png

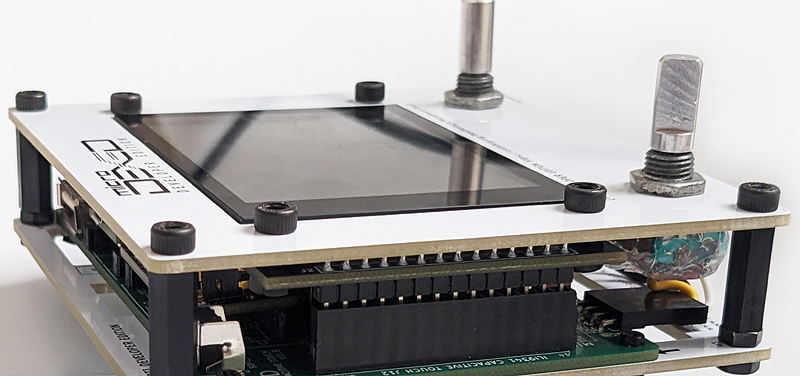
doc/Build_InstructionsV3_Capacitive_Touch/display_connector2.png
