propann/dexed/doc/Build_InstructionsV3_Capacitive_Touch/display_connector.png

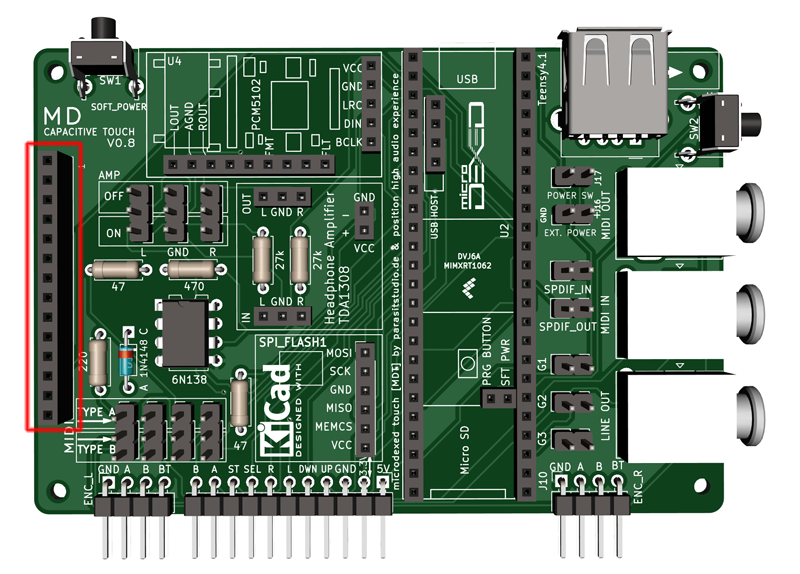
doc/Build_InstructionsV3_Capacitive_Touch/display_connector.png
