propann/dexed/doc/Build_InstructionsV3_Capacitive_Touch/jumper_amp_off.png

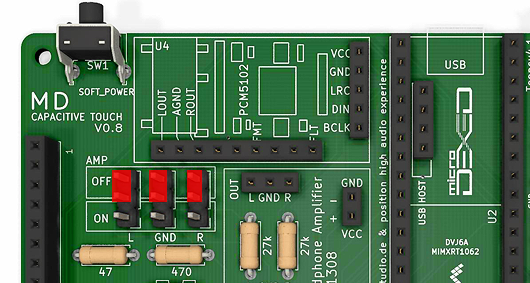
doc/Build_InstructionsV3_Capacitive_Touch/jumper_amp_off.png
