propann/dexed/doc/Build_InstructionsV3_Capacitive_Touch/jumper_midi_a.png

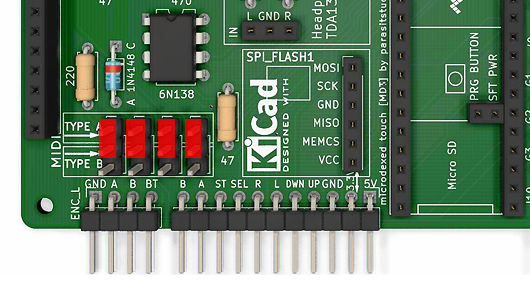
doc/Build_InstructionsV3_Capacitive_Touch/jumper_midi_a.png
