propann/dexed/doc/Build_InstructionsV3_Capacitive_Touch/jumper_none.png

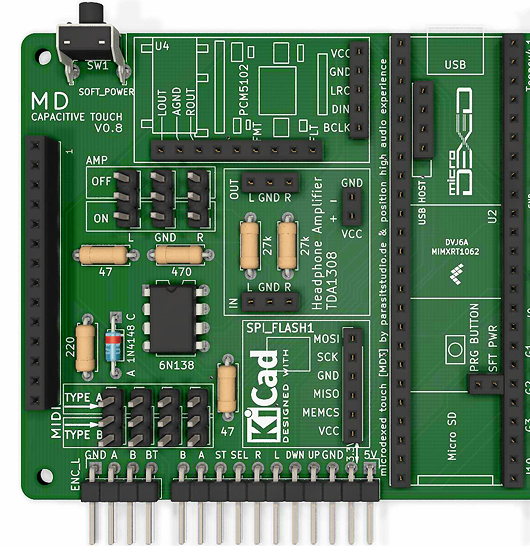
doc/Build_InstructionsV3_Capacitive_Touch/jumper_none.png
