propann/dexed/doc/Build_InstructionsV3_Capacitive_Touch/lid_nudge.png

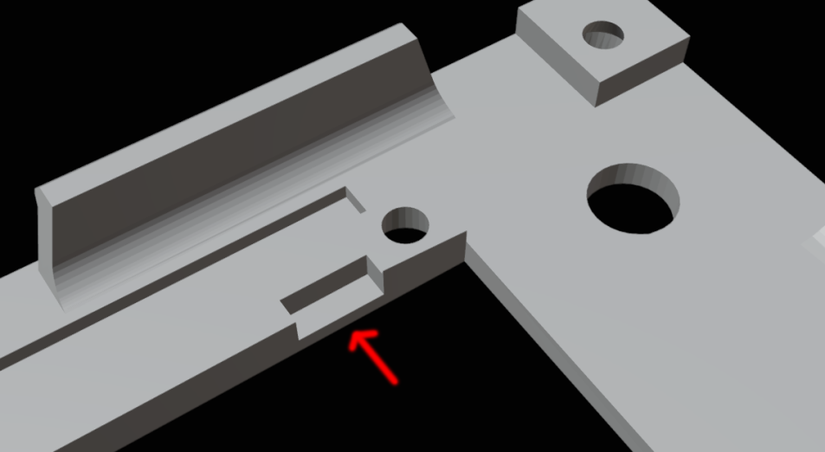
doc/Build_InstructionsV3_Capacitive_Touch/lid_nudge.png
