propann/dexed/doc/Build_InstructionsV3_Capacitive_Touch/lightbleed.jpg

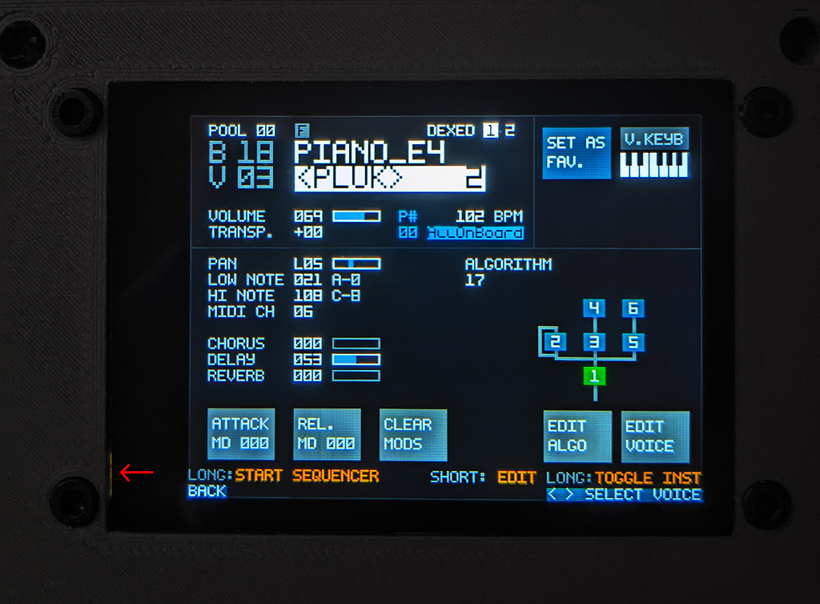
doc/Build_InstructionsV3_Capacitive_Touch/lightbleed.jpg
