propann/dexed/doc/Build_InstructionsV3_Capacitive_Touch/optional_pins.png

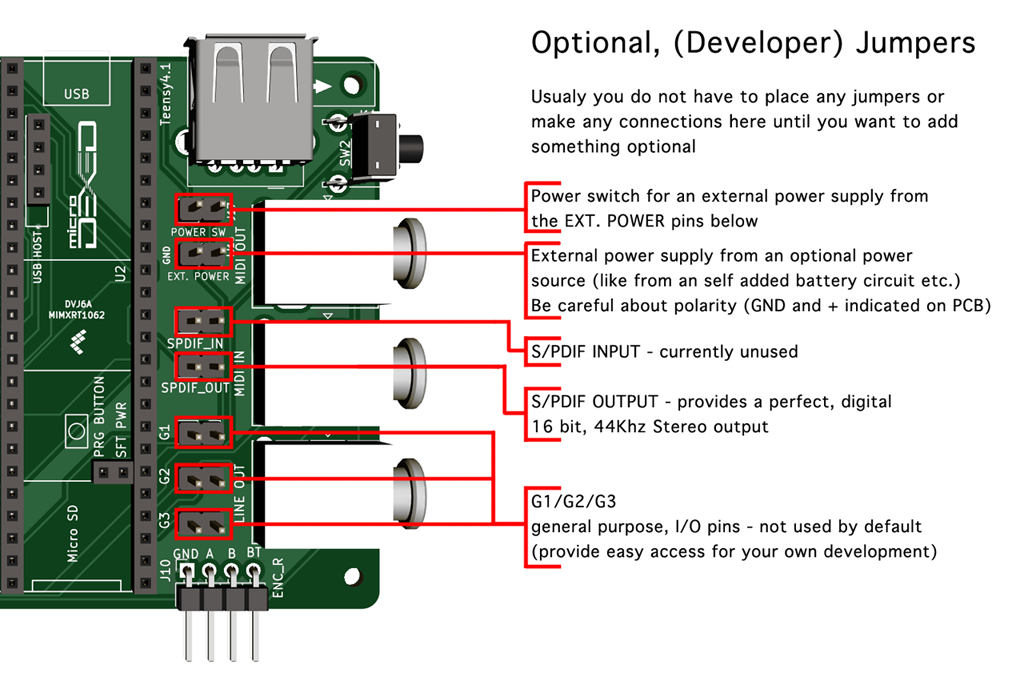
doc/Build_InstructionsV3_Capacitive_Touch/optional_pins.png
