propann/dexed/doc/Build_InstructionsV3_Capacitive_Touch/pcbway1.png

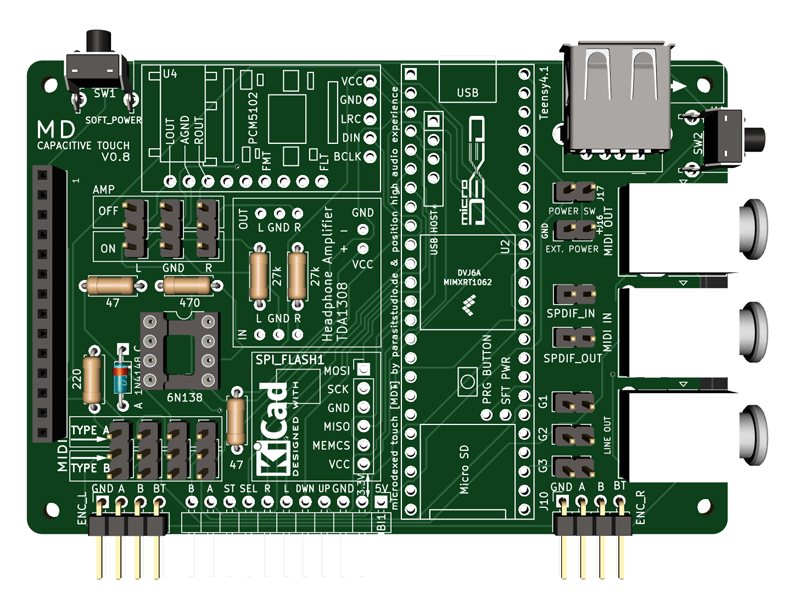
doc/Build_InstructionsV3_Capacitive_Touch/pcbway1.png
