propann/dexed/doc/complete_wiring.png

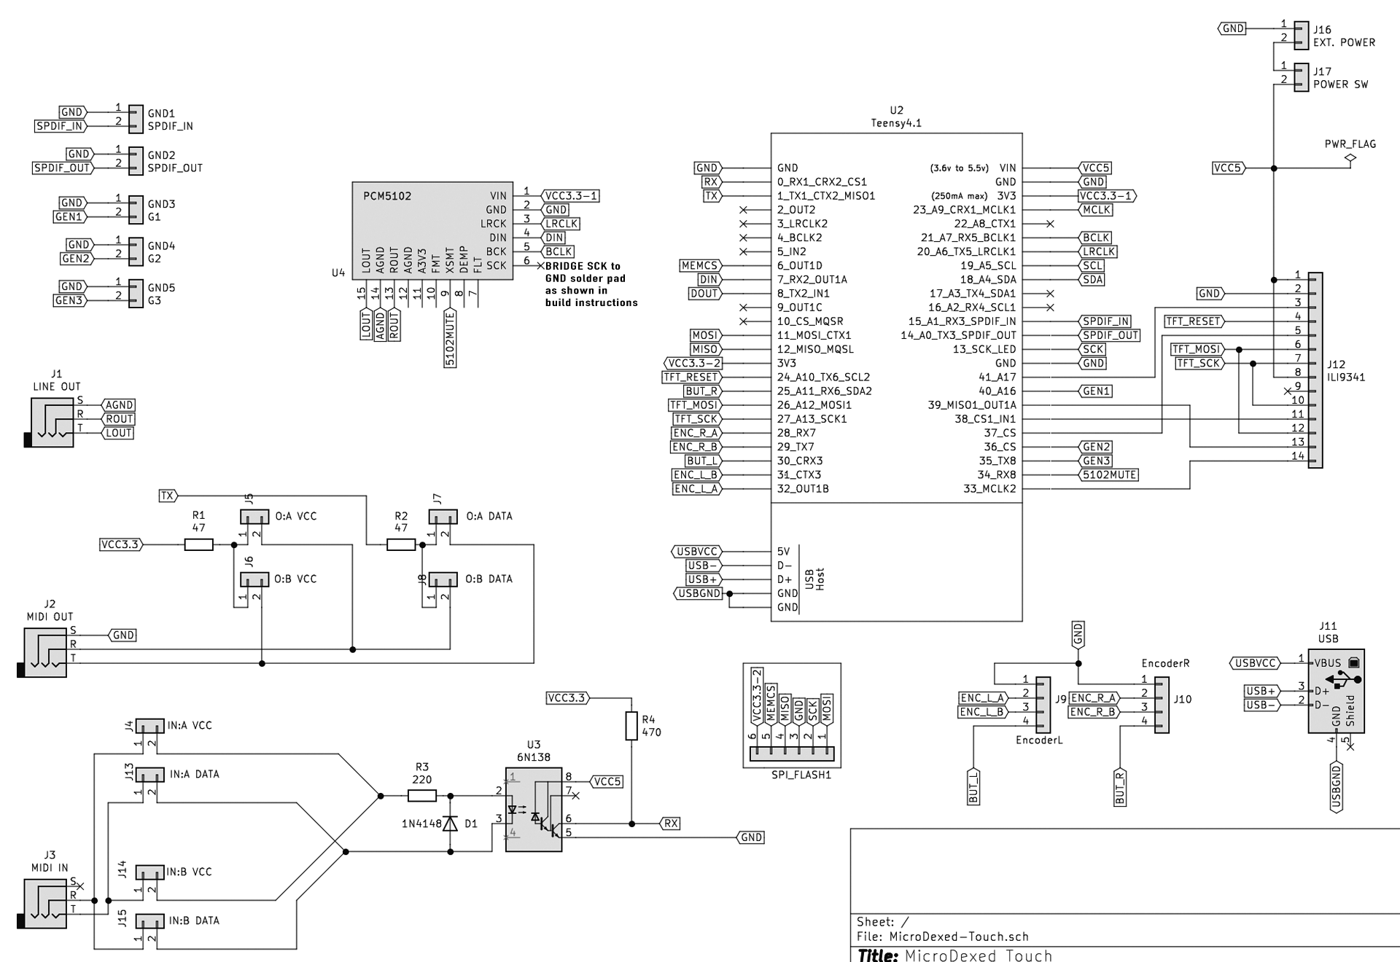
doc/complete_wiring.png
