propann/dexed/doc/Display-Conversion/wiring.jpg

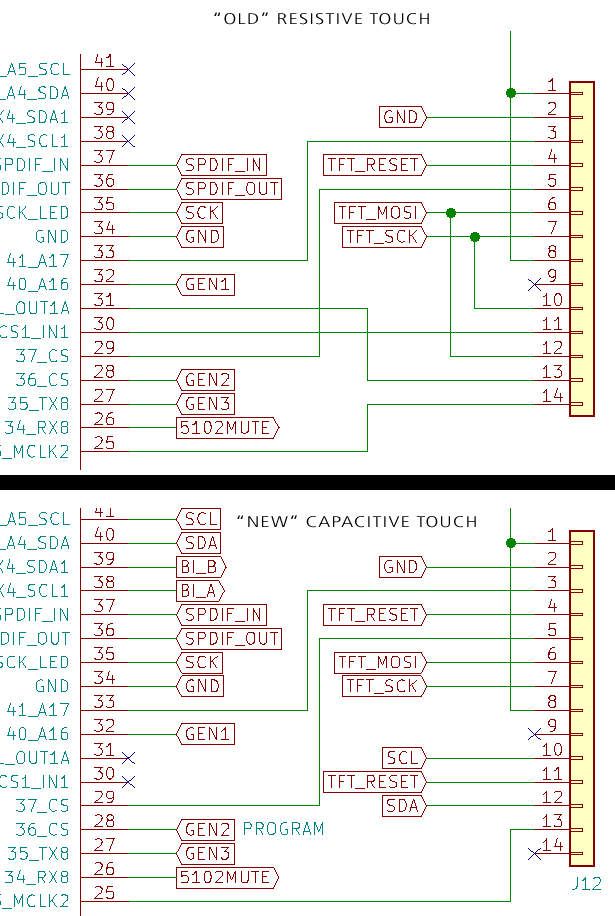
doc/Display-Conversion/wiring.jpg
