propann/dexed/doc/Gamepad/automap_step1.png

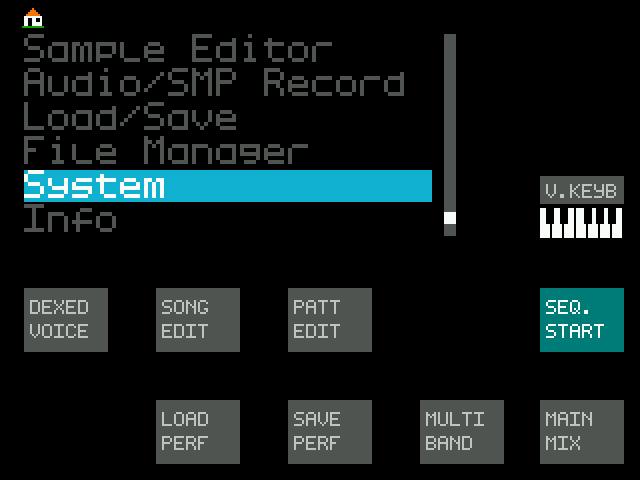
doc/Gamepad/automap_step1.png
