propann/dexed/doc/Gamepad/automap_step2.png

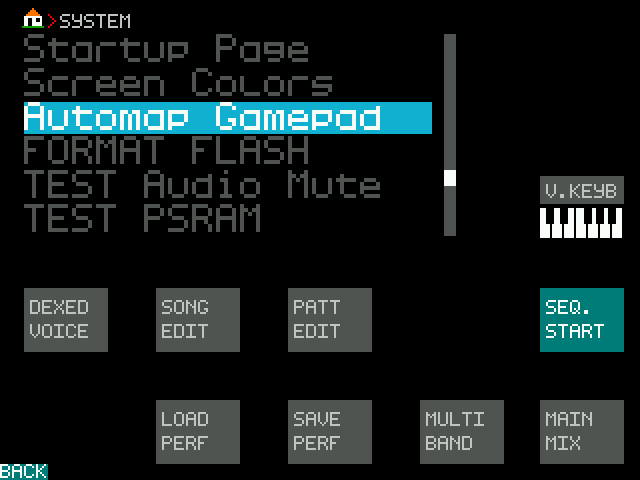
doc/Gamepad/automap_step2.png
