propann/dexed/doc/Gamepad/automap_step3.png

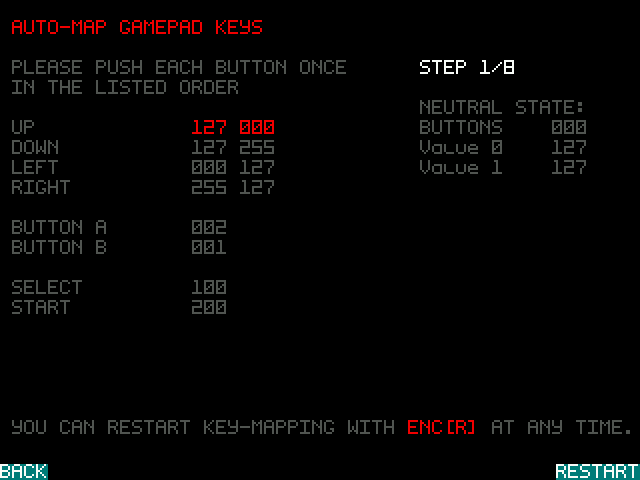
doc/Gamepad/automap_step3.png
