propann/dexed/doc/Gamepad/automap_step4.png

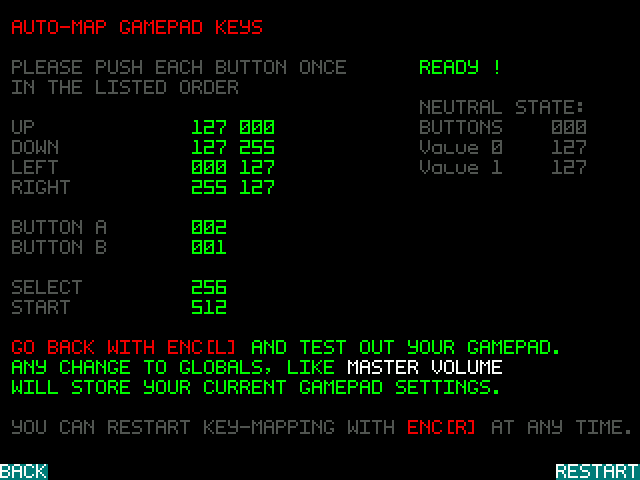
doc/Gamepad/automap_step4.png
