propann/dexed/doc/images/manual-images/OperationElements.png

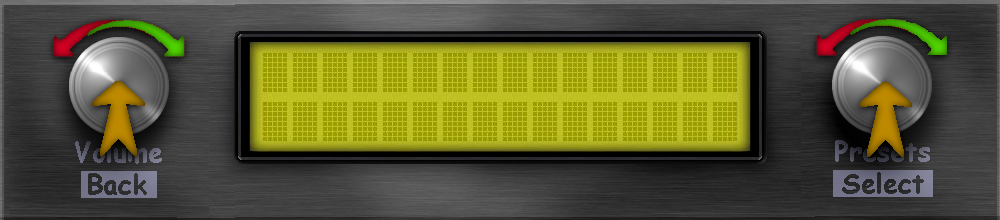
doc/images/manual-images/OperationElements.png
