propann/dexed/doc/images/manual-images/Volume_Left.png

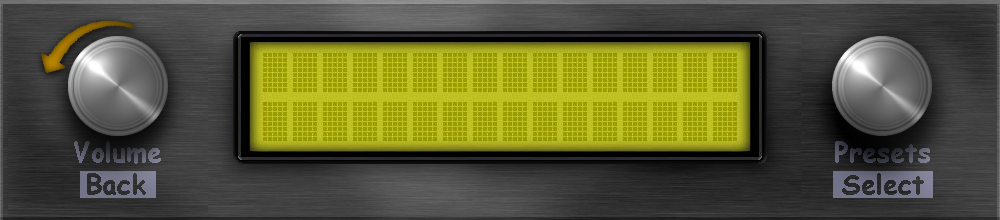
doc/images/manual-images/Volume_Left.png
