propann/dexed/doc/wiring-capacitive-touch.png

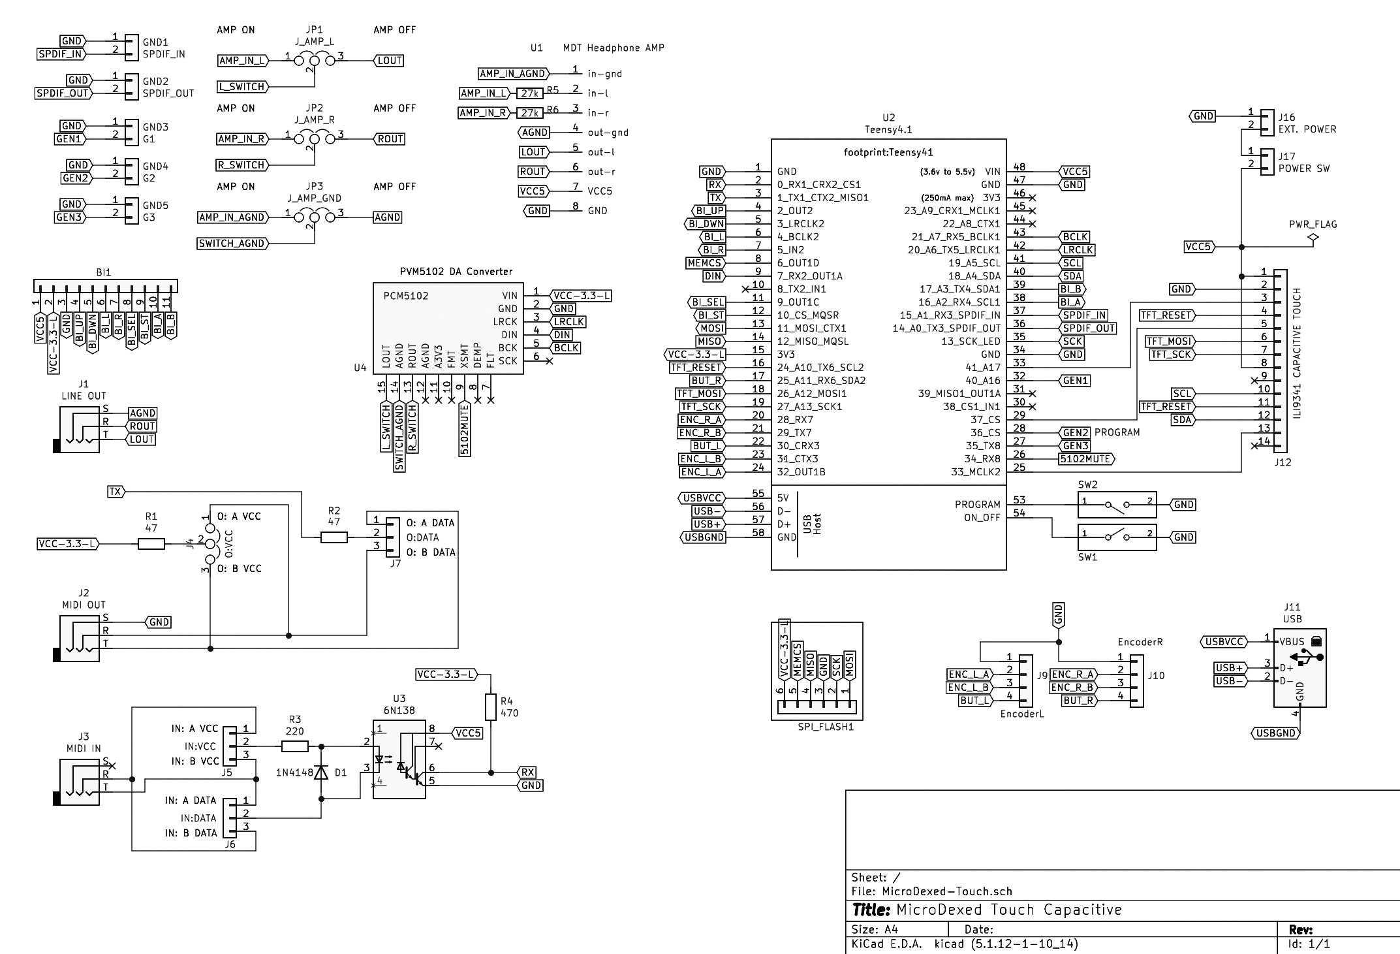
doc/wiring-capacitive-touch.png
